cfy2012/memoria-os/simulator/shots/simulator_mobile.jpg

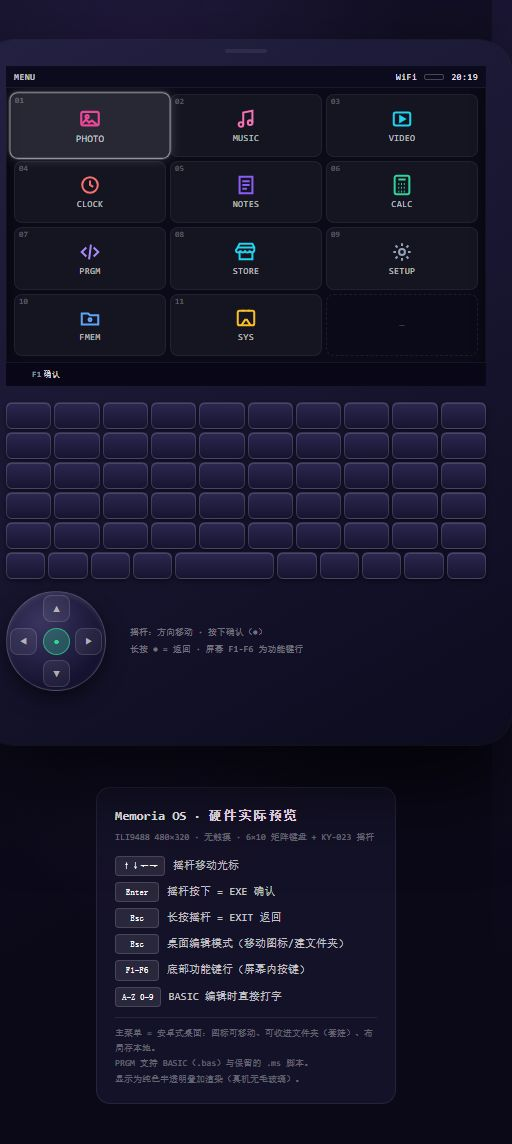
simulator/shots/simulator_mobile.jpg
