cfy2012/memoria-os/simulator/shots/simulator_desktop.jpg

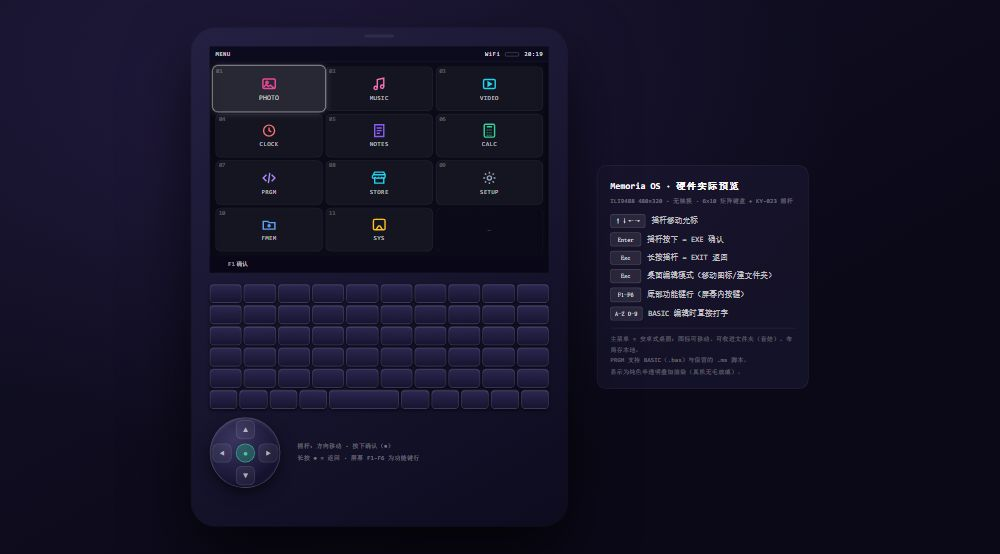
simulator/shots/simulator_desktop.jpg
