cfy2012/memoria-os/design/shell-design/Memoria-OS外壳尺寸规划.html

Memoria OS · HARDWARE SHELL · SPEC

# 外壳尺寸规划v7

ESP32-S3 掌机 · 2026-10-01 · 尺寸依据：HARDWARE-DIMENSIONS.md v7 · 引脚依据：components/memoria_drivers/include/drivers_config.hpp

核心板定版 摇杆甲案 KY-023 整机 ≈ 40.1mm 层间 2mm ×3

## 01关键尺寸

整机由 5 个实体层 + 3 条 2mm 悬空间隙叠成，屏幕面 → 背面。

40.1mm

整机厚度（设计值，38~42 区间）

2mm ×3

层间固定间隙（硬规则）

7.5mm

摇杆杆帽露出量

≥100 × 150mm

内腔净空（主板放置区）

## 02叠层剖面

每层高度 = 本层最高件（含板厚）；凸起元件收纳在本层内，不得侵占 2mm 间隙。实体隔板若加，每层 +1.6。

前面板

2.5

2

屏幕层

8

2

主板层

11.6

2

底仓

10

2

底壳

2

合计 ≈ 40.1mm（38~42 区间）
■ 主板层 11.6 = 洞洞板 1.6 + 摇杆机构 10（最高件）；核心板 5 / MCP23017 2.4 / TF 3 / TP4056 4 / 功放 5 / 灯带 2.5 全部收纳
■ 底仓 10 = 喇叭 8 + 腔体 2；锂电 5 平放
■ 屏幕层 8 = ILI9488 含排针（上限，实测可压到 6~7）

摇杆杆帽穿透（甲案 KY-023）

摇杆 PCB 面 → 前面板外表面 = 机构 10 + 间隙 2 + 屏幕层 8 + 间隙 2 + 面板 2.5 = 24.5mm 壳内贯通。
杆帽总高 32mm（自 PCB 面）→ 从前面板孔 Ø14~16 露出 7.5mm 作握持头。
屏幕 PCB 56×91 仅占屏幕层部分，摇杆走 PCB 侧边通道，不与屏体干涉；贯通路径上不得有金属屏蔽件。

ESP32 形态：核心板定版

S3-Zero 类核心板 18×27×4.5~5，插针/排母装配，免自焊 RF，自带屏蔽罩天线免净空区。
主板层独立小舱按 20×30 预留。模组直焊方案已弃用（需自焊 RF + 天线端 5mm 禁金属）。

## 03器件尺寸清单

典型值为市售模块通用规格，定稿前以卡尺实测为准（见 §07）。

器件 | 平面占位 | 高度 | 所在层 | 安装 | 外壳相关
ESP32-S3 核心板（S3-Zero 类）定版 | 18 × 27 | 4.5~5 | 主板层 | 插针/排母 | 小舱 20×30；免自焊 RF
ILI9488 3.5″ 屏模块 | PCB 56 × 91 | 6~8 含排针 | 屏幕层 | 排针插主板 | 视窗 70.8×48.5；屏幕窗 ≥71×49；务必实测
2× MCP23017（键盘扩展）最终定版 | 10.5 × 7.6 ×2 | 2.4 | 主板层 | 贴片/模块 | I2C 1/6，0x20/0x21，无 INT
轻触开关 6×6 矮款 ×60 | 6 × 6 | 2.5 | 主板层 | 直插 | 键中心距 10（≥9）；键孔 4.5×4.5
KY-023 摇杆高度约束 | PCB 26 × 34 | 板件 ~10 总高 ~32 | 主板层 | 直插 | 杆帽穿顶露出 7.5mm；面板孔 Ø14~16
MAX98357A 功放 | 15.5 × 13 | 4~5 | 主板层 | 模块 | 就近焊喇叭侧，引线短
喇叭 3W 4Ω | 23×35 或 20×30 | 5~10 +腔 2~3 | 底仓 | 粘/螺丝 | 透音孔开在喇叭正对面
TF 卡座（焊接式） | 15 × 16 | 2~3 | 主板层 | 焊接 | 卡外露 ≥4mm；侧缝 ≥13×2；可拆卸拔卡
SD 大卡槽（预留选项） | 30 × 29 | 3.5 | 主板层 | — | 侧缝 25×2.5；插卡行程 5mm；是否预留待定
TP4056 USB-C 充电模块 | 26.5 × 17.5 | 3~4 | 主板层 | 模块 | USB-C 凸出板边 1.5~2；侧孔 10×4
锂电聚合物 503450 级 | 50 × 34 | 5 | 底仓 | 松配 | 每边预留 1mm；仓按实物复核
WS2812 灯带 ×2 | 宽 10 | 2.5 | 主板层边缘 | 粘 | 每条 6 珠 ≈55mm；走线槽
电源拨动开关 SS12D00 | 19 × 10 | 7 含柄 | 侧壁 | — | 侧壁开槽 19×10；柄行程 4
主板洞洞板 | 100 × 150 | 板厚 1.6 | 主板层 | — | 元件层净高 ≤2

## 04前面板 / 侧壁开孔

全部开孔在壳体建模时按本表预留。

孔位 | 尺寸 | 位置 | 说明
屏幕窗 | ≥71 × 49 | 前面板 | 3.5″ ILI9488 480×320；实测视窗 +0.5
摇杆孔 | Ø14~16 | 前面板 | KY-023 杆帽穿顶贯通，露出 7.5mm
麦克风孔 | Ø1 × 2~3 | 前面板边缘 | INMP441 拾音（预留 GPIO45）
侧键孔 | ~20 × 3 | 侧壁 | 音量 / 电源
USB-C | 10 × 4 | 侧壁 | TP4056 充电口凸出 1.5~2
TF 卡 | ≥13 × 2 | 侧壁 | 卡外露 ≥4mm，可拆卸拔卡（字库/音频换卡）
SD 大卡槽（若预留） | 25 × 2.5 | 侧壁 | 插卡行程 5mm；待确认
电源开关槽 | 19 × 10 | 侧壁 | 柄行程 4mm
烧录口 / 排针孔 | 待定 | 侧壁或底壳 | UART 唯一烧录通道（43/44），必须预留
键盘键孔 | 4.5 × 4.5 ×60 | 前面板键盘区 | 6×10 布局，键中心距 10
喇叭透音孔 | 按喇叭面 | 底壳/侧壁 | 开在喇叭正对面

## 05GPIO / I2C 参考（迁移后）

引脚唯一来源：components/memoria_drivers/include/drivers_config.hpp。

功能 | GPIO | 说明
摇杆 X / Y | 7（ADC1_CH6）/ 5（ADC1_CH4） | 迁移后；旧 36/37 被 PSRAM 占
摇杆 BTN | 38 | 不动
电池 ADC | 4（ADC1_CH3） | 迁移后；旧 39 无 ADC
TF 卡 CS | 17 | 迁移后；旧 5
I2S BCLK / WS / DOUT | 18 / 21 / 15 | 迁移后；旧 4/3/2
SPI SCLK / MOSI / MISO | 12 / 11 / 13 | 不动
屏幕 CS / DC / RST / BLK | 10 / 9 / 8 / 14 | 不动
键盘灯带 | 46（RMT） | 不动
麦克风（预留） | 45 + 16/47（或 48） | INMP441；strapping 谨慎
USB D- / D+ | 19 / 20 | OTG 占用 → UART 为唯一烧录通道
UART0 TX / RX | 43 / 44 | 控制台 / 烧录
自由脚 | 16 / 47 / 48 + 40 / 41 / 42 | 可用 GPIO
永久不可用 | 26~32（Flash）、33~37（PSRAM） | 物理接不出

I2C 总线（I2C_NUM_0 @ GPIO1/6，400kHz）

0x20 / 0x21 = MCP23017 ×2（行+列C0-C3 / 列C4-C9）最终定版；
0x18 / 0x68 / 0x6B 预留段（新器件接线前请核对 I2C 地址占用）。

## 06装配顺序（底 → 顶）

5 步合壳，每层间留 2mm 悬空（支柱/卡扣），需要实体隔板时每层 +1.6。

1

#### 底壳 + 底仓

锂电 503450 平放（每边 1mm 松配）、喇叭 3W 定位，透音孔对正。

2

#### 主板层

洞洞板 100×150 固定；核心板插排母（小舱 20×30）；摇杆 KY-023 直插；MCP23017×2、TF 座、TP4056、MAX98357A、灯带走线槽。

3

#### 屏幕层

ILI9488 排针朝下插入主板对应排母，屏幕窗对位；摇杆杆帽走 PCB 侧边通道。

4

#### 前面板

60 键孔对位；摇杆杆帽从 Ø14~16 孔穿出，露出 7.5mm；屏幕窗合位。

5

#### 合盖 + 侧壁件

USB-C（10×4）、TF（≥13×2 外露 4mm）、电源开关槽、烧录口对孔；开机自检。

## 07待卡尺实测（定稿前必测）

以下 4 项是市售典型值，实际偏差会直接改变整机厚度或露出量。

- ILI9488 模块含排针实际高度 — 6~8mm，直接影响整机厚度 ±2mm （对应屏幕层 8）
- 喇叭实际厚度 + 腔体余量 — 5~10 + 2~3 （对应底仓 10）
- KY-023 杆帽立起实际总高 — 32±，偏差影响露出量 7.5± （对应摇杆穿顶）
- 电池实际厚度 — 503450 级典型 5，仓按实物复核 （对应底仓）

数据源：HARDWARE-DIMENSIONS.md v7 · components/memoria_drivers/include/drivers_config.hpp

Memoria OS · shell-design v7 · 2026-10-01
