cfy2012/memoria-os/docs/EASTER-EGGS-SPEC.md

# Memoria OS 彩蛋清单（Easter Eggs SPEC）

> 用途：给 GLM 实施用。共 100 条，时间线覆盖「送出之日 → 高一开学前」。
> **设计铁律（违反视为失败）**：
> 1. **发现式**——彩蛋是被使用者主动触发的，不是被推送的；
> 2. **非抢占**——任何彩蛋不得打断正在进行的操作，不得抢焦点、不得挡输入；
> 3. **可关闭**——设置页提供「彩蛋开关」，关掉后全部彩蛋失效；
> 4. 日期类彩蛋需 NVS 标记防重复（一年只触发一次），避免每次开机都弹。
> **受众口径**：使用者为同龄人（初三），**不以儿童视角设计**；文案平等、有梗、不幼稚。
> **暂缓项**：原「情人节画心」彩蛋按用户要求暂缓（赠礼双方为异性，语境不适用），未列入；后续如需启用由用户决定。

## 一、日期/时间触发（时间线彩蛋）17 条

| 编号 | 名称 | 触发方式 | 呈现效果 | 实现要点 |
|---|---|---|---|---|
| 1 | 首启欢迎 | 系统第一次开机 | 专属欢迎页「这是你的第二大脑」 | NVS 标记 has_booted，仅首次 |
| 2 | 第 7 天 | 累计开机天数 = 7 | 「你已经用它 7 天了」小横幅 | NVS 记 boot 计数 |
| 3 | 第 100 天 | 累计开机天数 = 100 | 计算器标题暂时显示「100 DAYS」 | NVS boot 计数 + 当天生效 |
| 4 | 万圣节 | 日期 10-31 | 图标南瓜/幽灵风一天；help 多一行 `trick or treat` | RTC 匹配 + 当日主题 |
| 5 | 平安夜 | 日期 12-24 | 时钟界面飘雪动画（纯氛围，不抢操作） | 时钟模式绘制雪粒子 |
| 6 | 圣诞 | 日期 12-25 | 圣诞配色一天 + 隐藏命令 `santa` | RTC + 主题色表 |
| 7 | 跨年 | 12-31 23:59 | 时钟界面倒计时，归零像素烟花 | 时钟模式专用分支 |
| 8 | 春节 | 农历正月初一（预置年份表） | 红色主题 + 隐藏命令 `红包` 随机文案 | 需农历年份映射表（GLM 配 2026/2027） |
| 9 | 清明 | 日期 4-04±1 | 当天首启显示「思」静默屏一秒 | 非抢操作，boot 横幅位 |
| 10 | 劳动节 | 日期 5-01 | 启动画面「劳动最光荣」 | boot 横幅位 |
| 11 | 青年节 | 日期 5-04 | 启动画面「少年自有少年狂」 | boot 横幅位 |
| 12 | 儿童节 | 日期 6-01 | 启动画面「今日份的少年感已到账」 | boot 横幅位（同龄口径，不低幼） |
| 13 | 端午 | 农历五月初五（预置年份表） | 粽子像素画彩蛋 | 农历映射表 |
| 14 | 中考倒计时 | 6 月 1 日 → 中考日 | 开机横幅「距离中考还有 N 天，稳住」 | 中考日期可配置（默认当地 6 月下旬） |
| 15 | 开学前 | 日期 8-31 | 隐藏命令 `要开学了` →「暑假余额不足」 | 隐藏命令即可，无需日期匹配 |
| 16 | 使用者生日 | 日期 2-01（默认预置，NVS 可改） | 开机横幅「生日快乐」+ 像素蛋糕（一年一次） | RTC 匹配 + NVS 年份标记 |
| 17 | 深夜关怀 | 23:00 后首次开机 | 「这么晚还不睡？明天上课」 | 时间匹配 + 一天一次 |

## 二、shell 隐藏命令（拉丁/致敬/内行梗）18 条

| 编号 | 名称 | 触发方式 | 呈现效果 | 实现要点 |
|---|---|---|---|---|
| 18 | memento | shell 敲 `memento` | 你写给使用者的寄语 | 隐藏命令，不进 help 清单 |
| 19 | carpe diem | shell 敲 `carpe diem` | 随机一句鼓励文案 | 随机文案池 |
| 20 | sapere aude | shell 敲 `sapere aude` | 显示系统源码总行数统计 | 编译期宏或运行时统计 |
| 21 | ad astra | shell 敲 `ad astra` | 星星 ASCII 动画 | 逐帧输出 |
| 22 | veni vidi vici | shell 敲 `veni vidi vici` | 成就音效 + 已解锁彩蛋计数 | 彩蛋解锁记录表 |
| 23 | fortune | shell 敲 `fortune` | 随机格言/毒鸡汤（致敬 Unix） | 文案池 |
| 24 | sudo | shell 敲 `sudo` | 「你已是最权限，不需要这个」 | 一条回复 |
| 25 | rm -rf / | shell 敲 `rm -rf /` | 「想让我自毁？不，我很稳」 | 拦截真实 rm，回复彩蛋 |
| 26 | reboot -f | shell 敲 `reboot -f` | 「没必要，我很稳定」 | 拦截回复 |
| 27 | hack | shell 敲 `hack` | 「你被监控了……开玩笑的，安全区」 | 一条回复 |
| 28 | matrix | shell 敲 `matrix` | 绿字数字雨数秒（伪矩阵） | 全屏随机字符动画，可按键退出 |
| 29 | ghost | shell 敲 `ghost` | 「你发现我了！」幽灵闪现 | 一条回复 + 幽灵字符 |
| 30 | ping | shell 敲 `ping` | 「pong！」（网络致敬） | 一条回复 |
| 31 | whoami | shell 敲 `whoami` | 「你是这台机器的主人」 | 一条回复 |
| 32 | 42 | shell 敲 `42` | 「生命、宇宙以及一切的答案」（银河系漫游指南梗） | 一条回复 |
| 33 | 404 | shell 敲 `404` | 「你要找的彩蛋不存在（或者它不想被发现）」 | 一条回复 |
| 34 | bug | shell 敲 `bug` | 「这是特性，不是 bug」 | 一条回复 |
| 35 | hello world | shell 敲 `hello world` | 「你好，世界。你好，你。」 | 一条回复 |
| 36 | hug | shell 敲 `hug` | 像素字符拥抱动画 + 「抱一下，辛苦了」 | 一条回复 + 字符画 |

## 三、按键/计算器彩蛋 10 条

| 编号 | 名称 | 触发方式 | 呈现效果 | 实现要点 |
|---|---|---|---|---|
| 37 | Konami 码 | 任意界面：上上下下左右左右 BA | 屏幕角出现小幽灵跟随光标 | 键盘/摇杆输入序列识别 |
| 38 | 强迫症检测 | 连按回车 5 次 | 「你是有强迫症吗？」 | 按键计数窗口 |
| 39 | hello | 计算器输入 `0.7734` | 显示 `hello, world` | 计算器特殊值 |
| 40 | 学习机声明 | 计算器输入 `58008` | 「你想多了，这是学习机」 | 计算器特殊值 |
| 41 | 中考年 | 计算器输入 `2027` | 「中考加油！」 | 计算器特殊值 |
| 42 | 光速 | 计算器输入 `299792458` | 「光速。跑得比光快的是你的思维」 | 计算器特殊值 |
| 43 | 隐藏音效 | 特定双键同按 3 秒 | 播放隐藏音效 | 按键组合长按检测 |
| 44 | 心事检测 | 音量+ 连按 7 次 | 「按了 7 次，有什么心事？」 | 按键计数 |
| 45 | 模式大师 | 快速切换 5 个模式 | 「模式大师」解锁画面 | 短时模式切换序列 |
| 46 | 隐藏秒表 | 时钟界面长按确认键 | 打开隐藏秒表 | 长按检测 + 秒表 UI |

## 四、界面/系统彩蛋 11 条

| 编号 | 名称 | 触发方式 | 呈现效果 | 实现要点 |
|---|---|---|---|---|
| 47 | 开发者名单 | 版本号界面连点 10 次 | 开发者名单 + 感谢语 | 点击计数 |
| 48 | logo 翻转 | About 页点 3 次 logo | logo 翻转/变色 | 点击计数 + 动画 |
| 49 | 满电侠 | 电量 100% 时开机 | 「满电侠」称号显示 | boot 读电量 |
| 50 | 连续作战勋章 | uptime ≥ 24h | 时钟界面一枚「连续工作 24h」勋章 | uptime 检查 |
| 51 | 隐藏模式 | SAFE MODE 敲 help | 多一行「你发现了隐藏模式」 | SAFE MODE help 分支 |
| 52 | 空目录哲学 | 空目录 ls | 「这里什么都没有，除了……」随机一句 | ls 空目录分支 |
| 53 | 测试检测 | 语言设置来回切 3 次 | 「你是在测试我吗？」 | 切换计数 |
| 54 | 温度提醒 | 右下角连点 5 次 | 「你很烫，注意休息」 | 点击计数 |
| 55 | 关机告别 | 电量 0% 关机前 | 「我没电了，晚安」 | 低电量关机钩子 |
| 56 | 用眼关怀 | 连续使用 3 小时 | 「该休息了，眼睛会疼」 | 连续使用计时 |
| 57 | 听力关怀 | 音量调到最大 | 「耳朵会疼的」 | 音量上限提示 |

## 五、文件/存储彩蛋 8 条

| 编号 | 名称 | 触发方式 | 呈现效果 | 实现要点 |
|---|---|---|---|---|
| 58 | 秘密信 | `ls -a` 看到 `.secret` 目录 | 里面一封写给使用者的信 | 预置隐藏目录（ls 默认过滤点开头） |
| 59 | 给未来的你 | 打开 `README_给未来的你.txt` | 「开学也要加油」 | 预置文件 |
| 60 | 命名吐槽 | 新建文件命名为「测试」 | 「你确定叫这个？」 | 文件名检测 |
| 61 | 作业雷达 | 新建文件命名为「作业」 | 「在系统里找作业？写作业去吧」 | 文件名检测 |
| 62 | 系统自嘲 | 打开特殊命名文件夹（`.` 别名） | 系统自嘲文案 | 特殊路径拦截 |
| 63 | 温度确认 | 删除文件时二次确认 | 「这个文件可能很重要」 | 正常功能带温度文案 |
| 64 | 别打开 | 打开 `.do_not_open` 文件 | 「都说了别打开」 | 预置文件 + 名称拦截 |
| 65 | 彩蛋引导 | 存储使用率 ≥ 99% | 「清理一下，顺便看看 `.secret` 目录」 | 存储检查 + 引导提示 |

## 六、二十四节气彩蛋 24 条

| 编号 | 名称 | 触发方式 | 呈现效果 | 实现要点 |
|---|---|---|---|---|
| 66 | 立春 | 2-03/2-04 | 启动横幅「立春 · 万物生」 | 节气日期表（公历范围） |
| 67 | 雨水 | 2-18/2-19 | 「雨水 · 好雨知时节」 | 节气日期表 |
| 68 | 惊蛰 | 3-05/3-06 | 「惊蛰 · 春雷动，万物醒」 | 节气日期表 |
| 69 | 春分 | 3-20/3-21 | 「春分 · 昼夜平分」 | 节气日期表 |
| 70 | 清明 | 4-04/4-05 | 「清明 · 雨纷纷」 | 与 9 号同日，实施合并：静默屏 + 节气文案，一天一次 |
| 71 | 谷雨 | 4-19/4-20 | 「谷雨 · 雨生百谷」 | 节气日期表 |
| 72 | 立夏 | 5-05/5-06 | 「立夏 · 夏木成阴」 | 节气日期表 |
| 73 | 小满 | 5-20/5-21 | 「小满 · 物致于此小得盈满」 | 节气日期表 |
| 74 | 芒种 | 6-05/6-06 | 「芒种 · 有芒之种」 | 节气日期表 |
| 75 | 夏至 | 6-21/6-22 | 「夏至 · 日长之至」 | 节气日期表 |
| 76 | 小暑 | 7-06/7-07 | 「小暑 · 温风至」 | 节气日期表 |
| 77 | 大暑 | 7-22/7-23 | 「大暑 · 大热」 | 节气日期表 |
| 78 | 立秋 | 8-07/8-08 | 「立秋 · 秋至」 | 节气日期表 |
| 79 | 处暑 | 8-22/8-23 | 「处暑 · 出暑」 | 节气日期表 |
| 80 | 白露 | 9-07/9-08 | 「白露 · 露从今夜白」 | 节气日期表 |
| 81 | 秋分 | 9-22/9-23 | 「秋分 · 平分秋色」 | 节气日期表 |
| 82 | 寒露 | 10-07/10-08 | 「寒露 · 露寒而凝」 | 节气日期表 |
| 83 | 霜降 | 10-23/10-24 | 「霜降 · 气肃而凝」 | 节气日期表 |
| 84 | 立冬 | 11-07/11-08 | 「立冬 · 水始冰」 | 节气日期表 |
| 85 | 小雪 | 11-22/11-23 | 「小雪 · 未盛为雪」 | 节气日期表 |
| 86 | 大雪 | 12-06/12-07 | 「大雪 · 至此而雪盛」 | 节气日期表 |
| 87 | 冬至 | 12-21/12-22 | 「冬至 · 冬至不端饺子碗，冻掉耳朵没人管」 | 节气日期表（北方梗） |
| 88 | 小寒 | 1-05/1-06 | 「小寒 · 雁北乡」 | 节气日期表 |
| 89 | 大寒 | 1-20/1-21 | 「大寒 · 至此极」 | 节气日期表 |

## 七、模式专属彩蛋 6 条

| 编号 | 名称 | 触发方式 | 呈现效果 | 实现要点 |
|---|---|---|---|---|
| 90 | 整点报时 | 时钟模式每逢整点 | 「X 点整」+ 可选音效 | 整点检测，轻量，不抢操作 |
| 91 | 单曲计数 | 音乐模式同一首歌播放 ≥3 次 | 「这首你听了 N 遍了」 | NVS 播放计数 |
| 92 | 照片故事 | 照片模式查看特定日期（如送出日）的照片 | 「这天有故事」 | 文件名/EXIF 日期匹配 |
| 93 | 秘密程序 | 编程模式运行 `secret.bas` | 隐藏程序：像素动画 | 预置脚本 + 名称拦截 |
| 94 | 隐藏商品 | 商店模式出现 0 元商品「开发者纪念头像」 | 可购买收藏 | 商店数据预置 |
| 95 | 笔记彩蛋 | 笔记标题输入「memento」 | 套用隐藏模板（一句寄语） | 标题关键词匹配 |

## 八、成就系统彩蛋 5 条

| 编号 | 名称 | 触发方式 | 呈现效果 | 实现要点 |
|---|---|---|---|---|
| 96 | 百炼成钢 | 累计开机 100 次 | 「百炼成钢」成就 | NVS 开机计数 |
| 97 | 键盘侠 | 累计敲命令 1000 次 | 「键盘侠」成就 | NVS 命令计数 |
| 98 | 全勤奖 | 连续 7 天开机 | 「全勤奖」成就 | NVS 日期链检测 |
| 99 | 寻宝猎人 | 解锁彩蛋 ≥ 10 个 | 「寻宝猎人」称号 | 解锁记录表 |
| 100 | 满级大佬 | 解锁全部彩蛋 | 「你已经找到所有秘密」+ 最后一封信 | 全解锁检测 |

## 实施说明

- **农历节日（8/13）**：GLM 需配 2026/2027 年份农历映射表（春节、端午具体公历日期），RTC 公历日期查表触发。
- **中考倒计时（14）**：中考日期做成可配置字段（NVS/配置文件），默认按当地中考时间（2027 年 6 月下旬）；提前 30 天进入倒计时窗口，只显示一次/天。
- **NVS 防重复**：所有日期类彩蛋配「年份已触发」标记，防止一天内多次重启反复弹出；生日彩蛋单独按年份标记；深夜关怀（17）按「当天已触发」标记。
- **优先级**：以上均属低优先级、纯增量模块，建议在系统主线稳定（240MHz 验收完成、教材/手册同步完成）后排期实施。
- **彩蛋开关**：设置页加「彩蛋」开关，默认开；关闭后隐藏命令返回 unknown command，日期类不触发，按键类不识别。
- **口径**：所有文案按同龄人（初三）平等语气撰写，杜绝「小朋友」「乖」等低幼表述；发现者读到的是「伙伴」，不是「长辈」。

## 验收口径

1. 彩蛋开关关闭后，全部 64 条失效；
2. 任何彩蛋不得阻塞正在进行的操作（渲染/输入/任务）；
3. 日期类彩蛋一年内同一天只出现一次；
4. 隐藏命令不在 help 清单出现（51 号彩蛋除外，它自己就是被发现项）；
5. 全部文案通过「同龄人口径」审查：无低幼化、无性别敏感内容；
6. 节气彩蛋 24 条全年覆盖，与日期类彩蛋同天时合并为一次触发（如清明）；
7. 成就系统依赖 NVS 解锁记录表，与 22 号（veni vidi vici）共用同一计数。
