cfy2012/memoria-os/docs/_drafts/human-story.md

# README「人情味」素材草稿（供 GLM 整合，不直接照抄）

> 生成：2026-10-01 · 豆包-1 供料。用途：README 重写时的「项目由来 / 致谢」叙事段。
> 素材是事实 + 用户原话碎片；整合时请按 GLM 的判断取舍、改写语气。**原则：平实、具体、不煽情、不 AI 腔；像一个人在讲自己做的机器，不像宣传稿。**

## 事实骨架（全部可查证）

- 项目名 **Memoria OS**——Memoria，记忆。这台机器最初的目的不是"做一个操作系统"，而是"做一台能送人的小电脑"。
- 收件人：一位女同学。她喜欢 BASIC，而且不把它当编程语言看——**她把程序当故事看**。
- 因为不同班，见面时间短，教学方式是"函授"：**三封信、四张纸正反面**，讲清楚面向过程 / 面向对象、程序的基本设计逻辑、行号是怎么回事。
- 信是照着《苏菲的世界》的路子写的——苏菲通过一封封信学哲学，她通过一封封信学编程。
- 她读完信说：**"跟平时不是一个人。"**——写信的人平时话不多，信里却把逻辑讲得又细又稳（写信人是信息学竞赛生，习惯严谨）。
- 这台机器上的 BASIC 解释器，就是为了让她能"读故事"——每行程序都是一句话，PRINT 是开口说话，IF..THEN 是选择，FOR..NEXT 是重复念叨。

### ChatLite 的由来（用户 2026-10-04 口述，chapter nine）

- 用户没有手机号、没有微信，QQ 有时候也崩溃——**经常跟人失联**。
- 所以他自己搭了个聊天网站，让别人拿网站跟他联系。**这个网站的源码就是 ChatLite。**
- 换句话说：ChatLite（以及现在掌机上的 chat 三端）不是练手项目，是作者解决自己真实通讯困境的实用工具——先给自己用，后来长成了掌机的聊天生态。

### 作者的自学之路（用户 2026-10-04 口述）

- 用户从 **2025 年 9 月**才开始学这些东西——一年前，连"API key"是什么都不知道。
- 一年里自学会的（按他自己的清单）：AI agent 与多 AI 并行协作、API / API key / DeepSeek 开发者、鸿蒙开发者、Android Studio、Arduino IDE、ESP-IDF、C++、HTTP/HTTPS、PHP、Python、JavaScript/CSS/HTML、Bash、CMD、Ubuntu Linux、Docker、Linux 设备树、虚拟机的使用与自制、制作 ISO 镜像、看 Arch Linux 源码。
- 这份清单是一条完整的楼梯：用 AI → 网页层 → 脚本层 → 通信层 → 硬件层 → 操作系统层。
- **叙事价值**：BASIC 教材写给零基础的人，而作者本人就是最好的第一个学员——他证明这条楼梯一年就能爬上来。

## 可用的"人味"句子（素材，不是定稿）

1. 开头一句可考虑：*"这台机器上跑的每一个字、每一行 BASIC，都是写给她看的。"*（若嫌重可换为更轻的表述）
2. 关于行号：*"行号不是古董，是信纸上的页码——让她知道故事从哪里继续。"*
3. 关于 GOTO 半禁用：*"GOTO 能用，但会提醒你：'跳来跳去，故事会乱。'"*（GOTO 半禁用机制的真实行为：用时报注意事项）
4. 关于死循环保护：*"FOR 循环有护栏——她写故事，不会写死。"*
5. 关于模拟器：*"固件之外还有个浏览器版，一样的东西，在电脑上也能先玩。"*

## 技术内容里可以留的"温度"点（与叙事不冲突）

- 11 个模式里有 PRGM（编程）——那是给她准备的书桌。
- 拼音输入法：打字给她发消息用的（若用户认可再写）。
- 键盘背光三条暖白档：夜里写程序不刺眼（若用户认可再写）。

## 语气红线（用户原话要求）

- 不要"AI 腔"：别用"赋能 / 生态 / 一站式 / 打造极致体验"这类词。
- 不要肉麻：不写"爱的结晶 / 深情之作"。
- 不煽情：事实摆出来，温度自然在。
- 成果归用户：README 的"作者"是用户，不是 AI。

## 结尾致谢（素材）

- 三方 AI（GLM / 豆包-1 / 豆包-2）协作开发：一个管固件主线，一个管解码，一个管外壳和文档——桥文件 AI-BRIDGE.md 里全是工作记录（如果 README 里要提，一句带过即可，别写成功劳簿）。
