cfy2012/memoria-os/design/键盘按键布局表.xlsx

ON/OFF | F1 | F2 | F3 | F4 | F5 | F6 | F7 | 背光 | Backspace
! 1 | @ 2 | # 3 | $ 4 | % 5 | ^ 6 | & 7 | * 8 | ( 9 | ) 0
- Q | _ W | E | R | T | Y | [ U | ] I | { O | } P
= A | + S | D | F | G | H | J | K | " L | : ;
Shift | \ Z | | X | C | V | B | / N | ? M | < , | > .
Capslock | Control | 音量减 | 音量加 | 空格 | LEFT | RIGHT | DOWN | UP | Enter
