cfy2012/memoria-os/docs/audio-guard/AudioGuard-最坏情况模拟.png

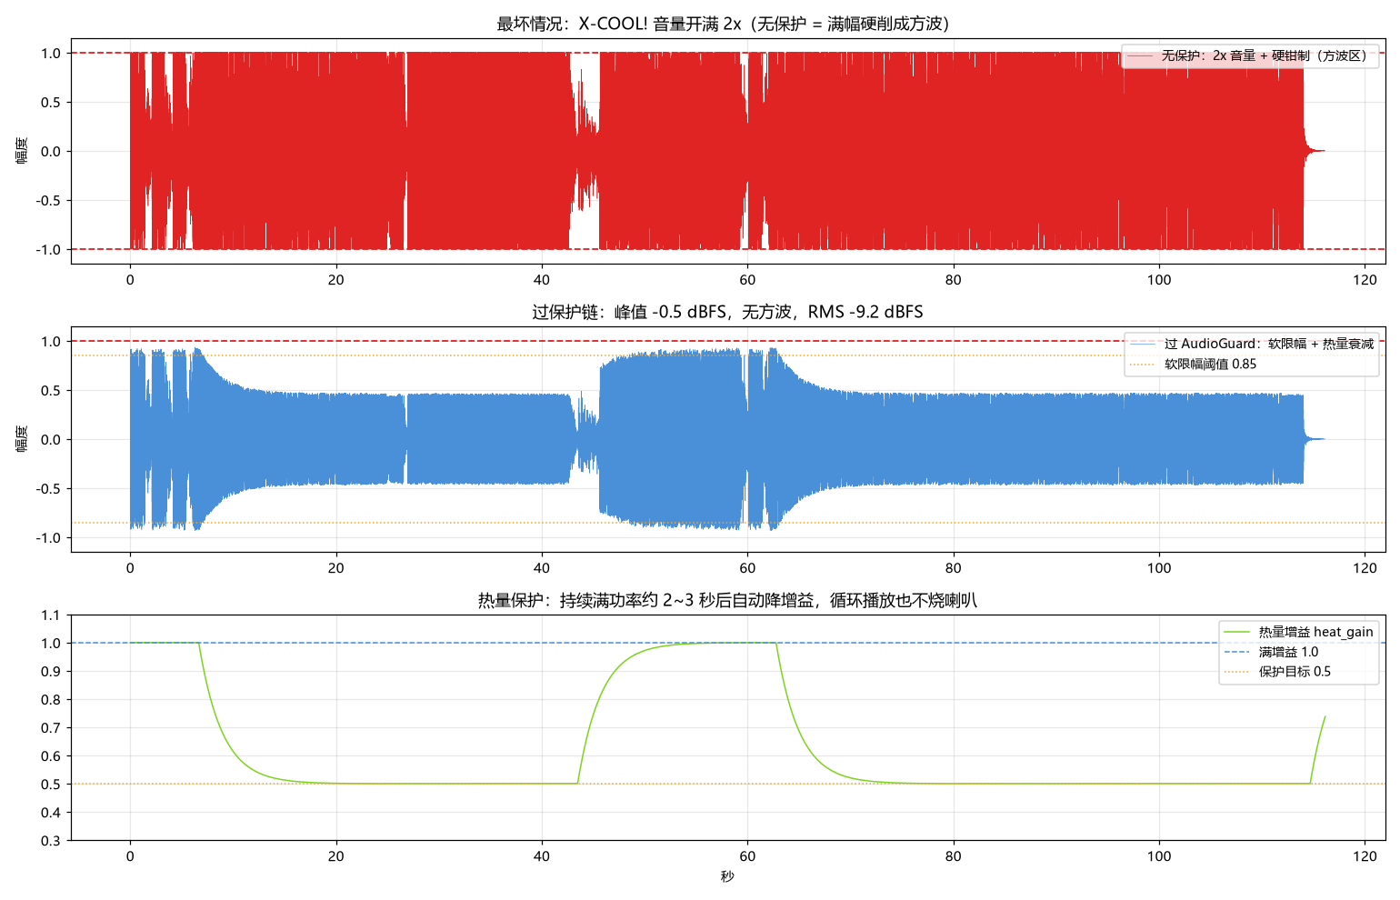
docs/audio-guard/AudioGuard-最坏情况模拟.png
