cfy2012/memoria-os/docs/audio-guard/BATIDAO-FUNK-波形分析.png

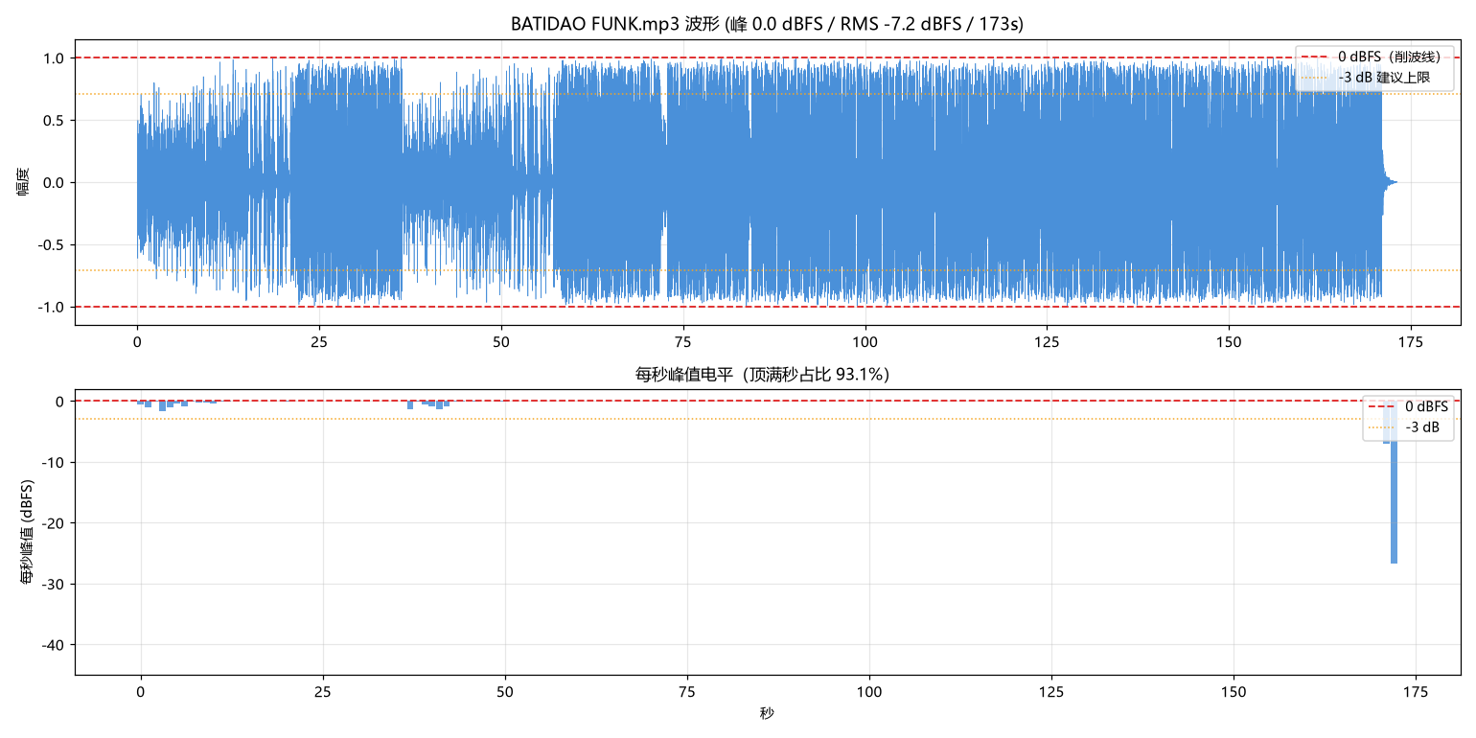
docs/audio-guard/BATIDAO-FUNK-波形分析.png
