cfy2012/memoria-os/docs/audio-guard/DANÇA-DO-VERÃO-波形分析.png

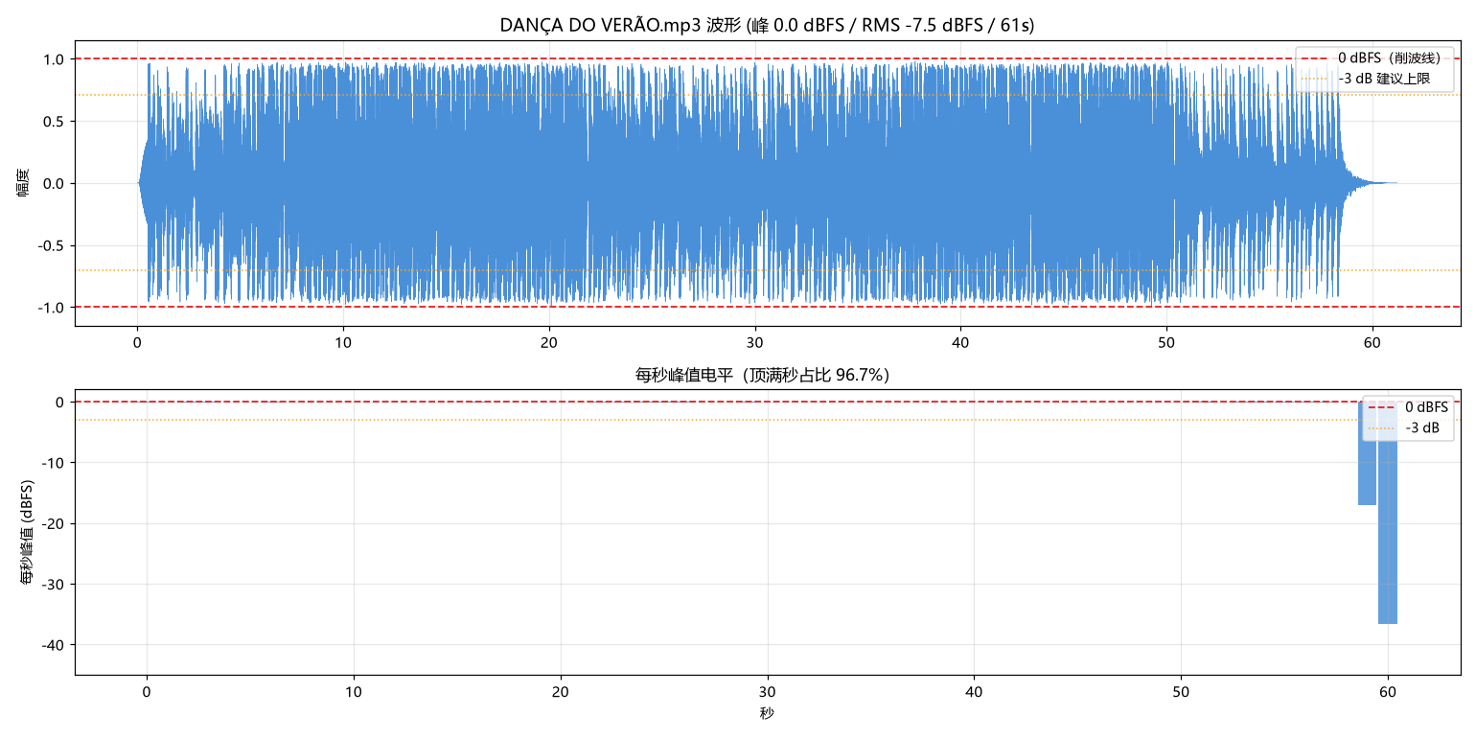
docs/audio-guard/DANÇA-DO-VERÃO-波形分析.png
