cfy2012/memoria-os/docs/audio-guard/De-Natal-波形分析.png

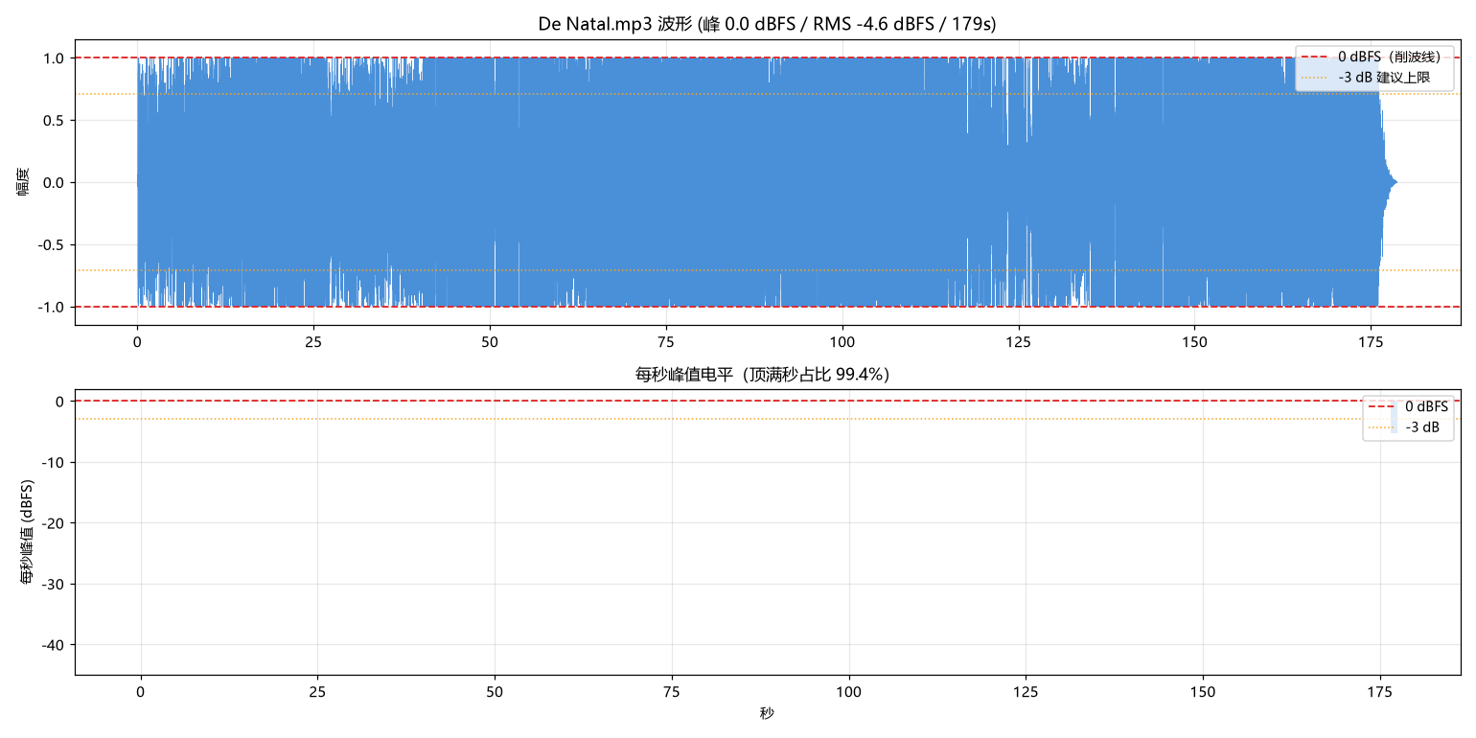
docs/audio-guard/De-Natal-波形分析.png
