cfy2012/memoria-os/docs/audio-guard/DREAMFUNK-波形分析.png

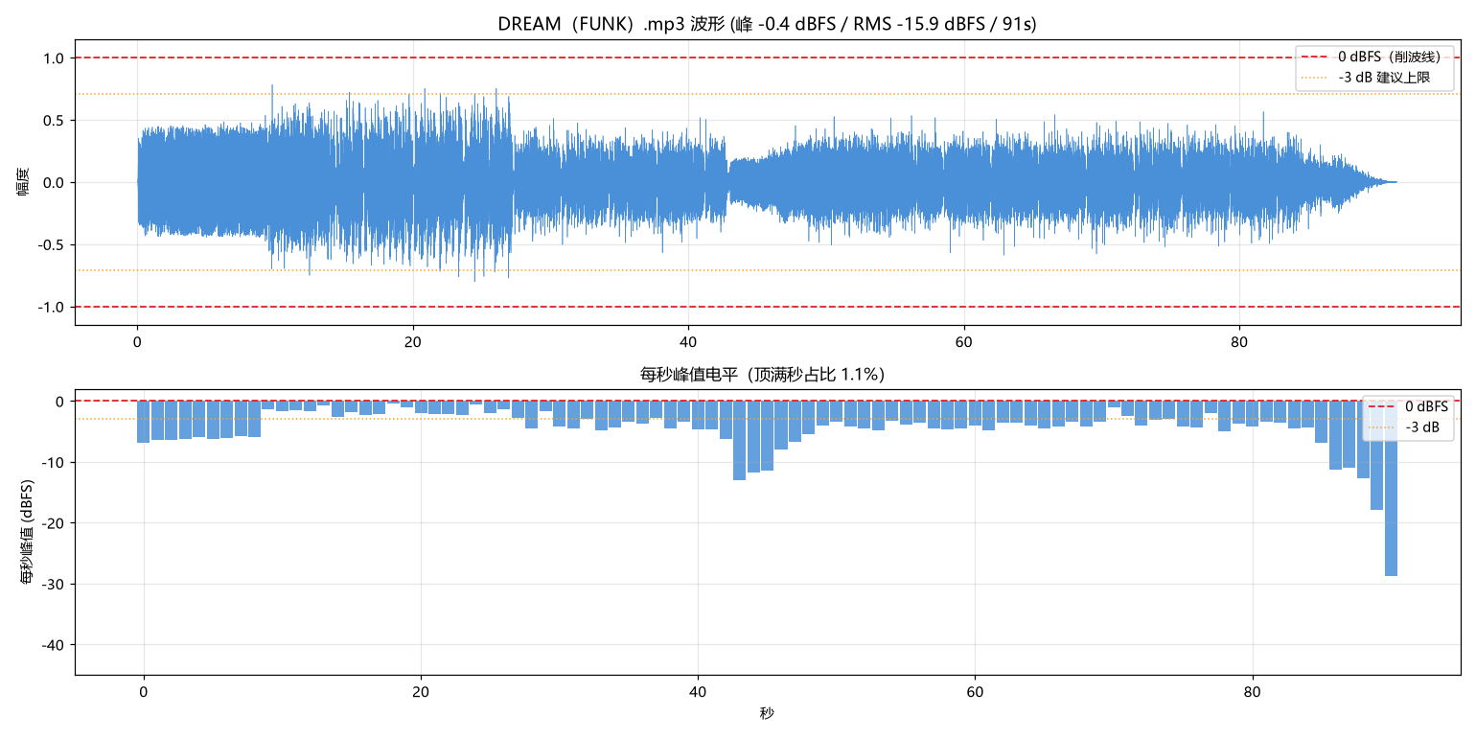
docs/audio-guard/DREAMFUNK-波形分析.png
