cfy2012/memoria-os/docs/audio-guard/FAVELA-波形分析.png

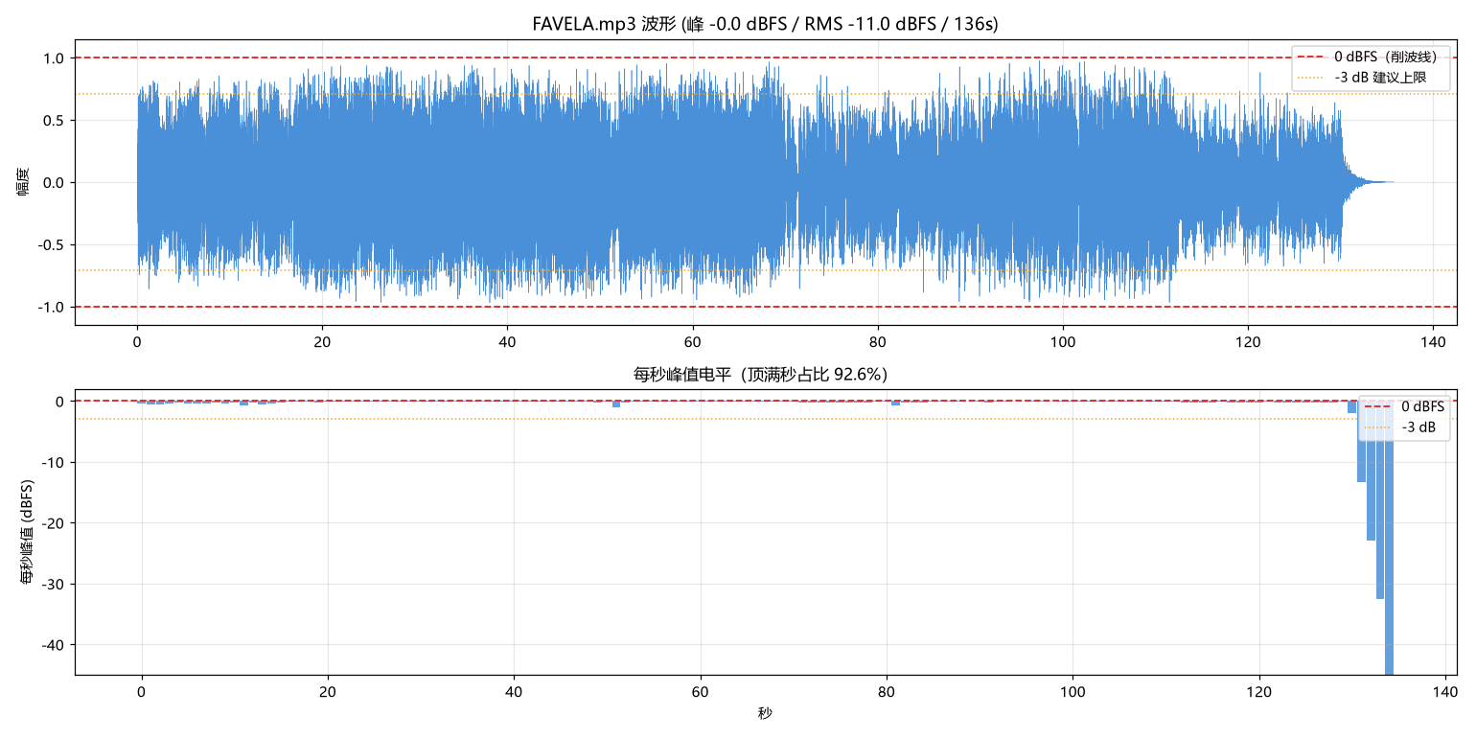
docs/audio-guard/FAVELA-波形分析.png
