cfy2012/memoria-os/docs/audio-guard/FREQUÊNCIA-波形分析.png

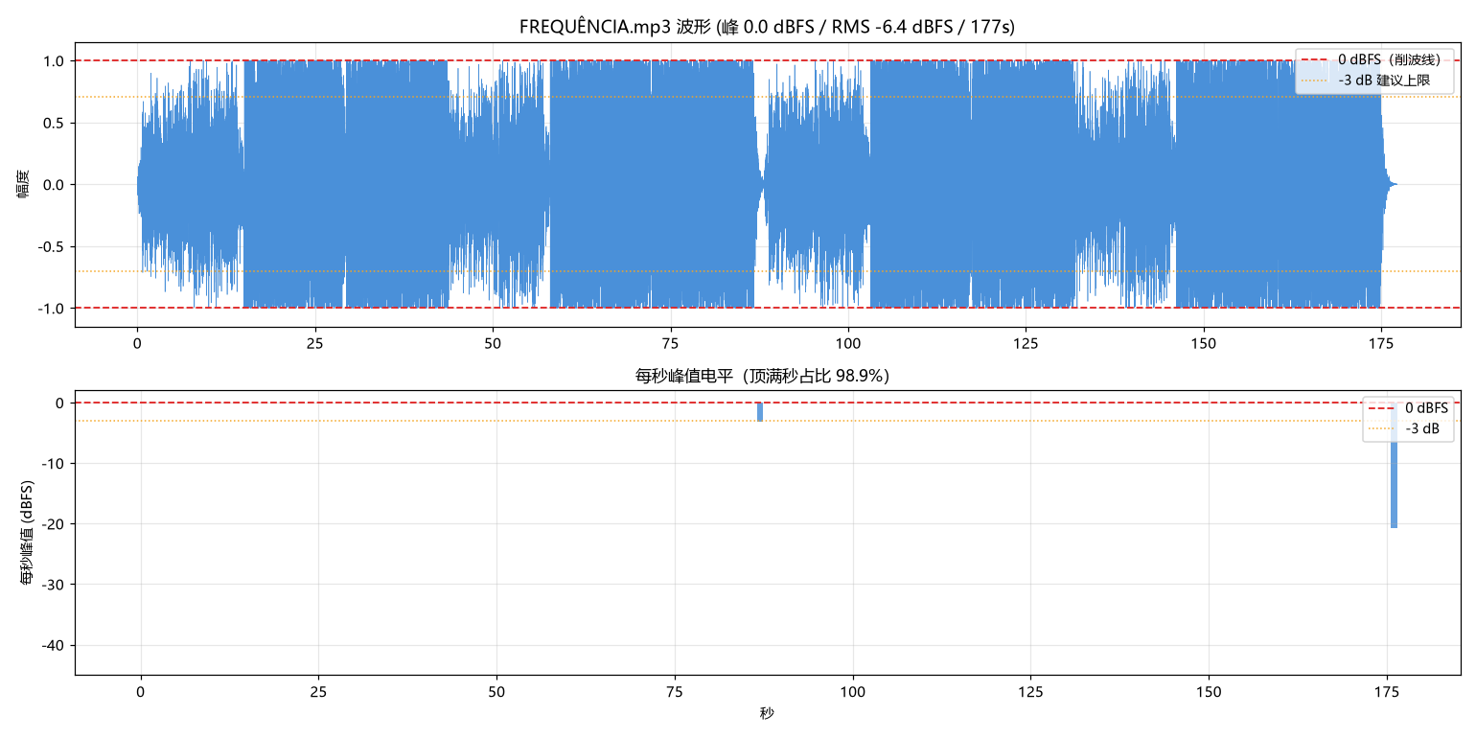
docs/audio-guard/FREQUÊNCIA-波形分析.png
