cfy2012/memoria-os/docs/audio-guard/HEAVENLY-JUMPSTYLE-波形分析.png

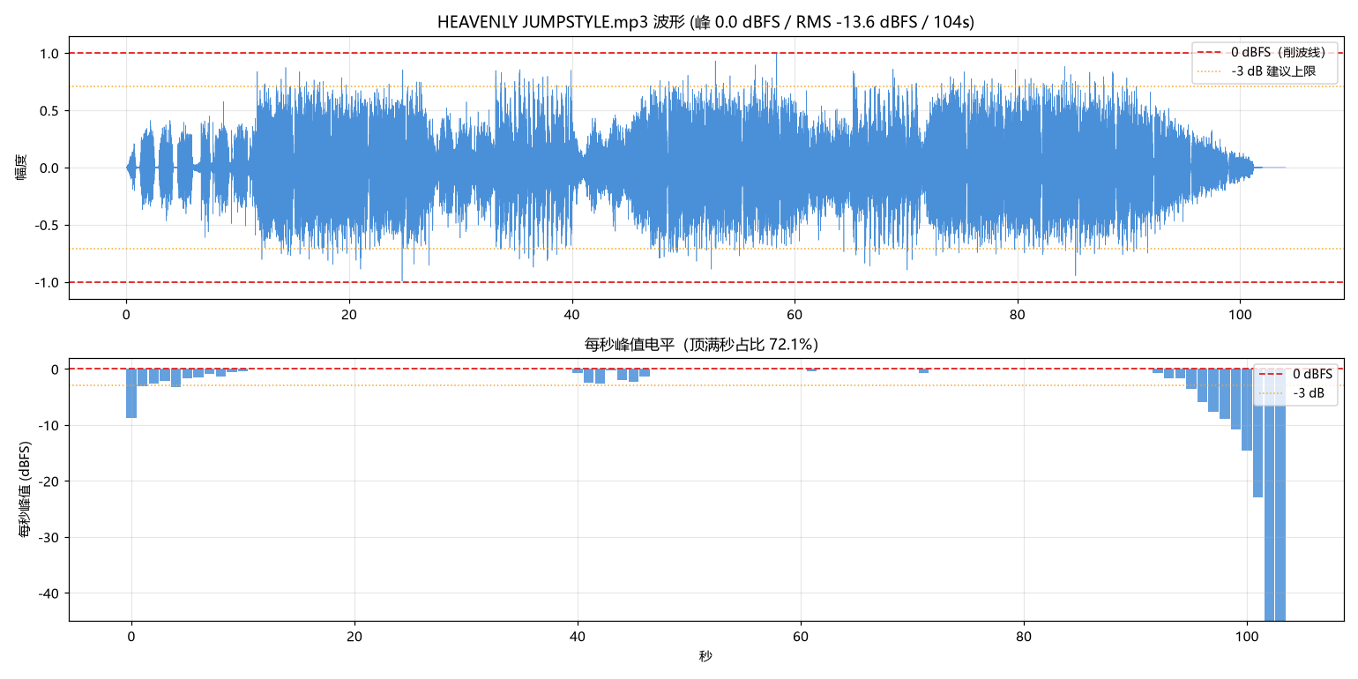
docs/audio-guard/HEAVENLY-JUMPSTYLE-波形分析.png
