cfy2012/memoria-os/docs/audio-guard/HOMAGE-FUNK-波形分析.png

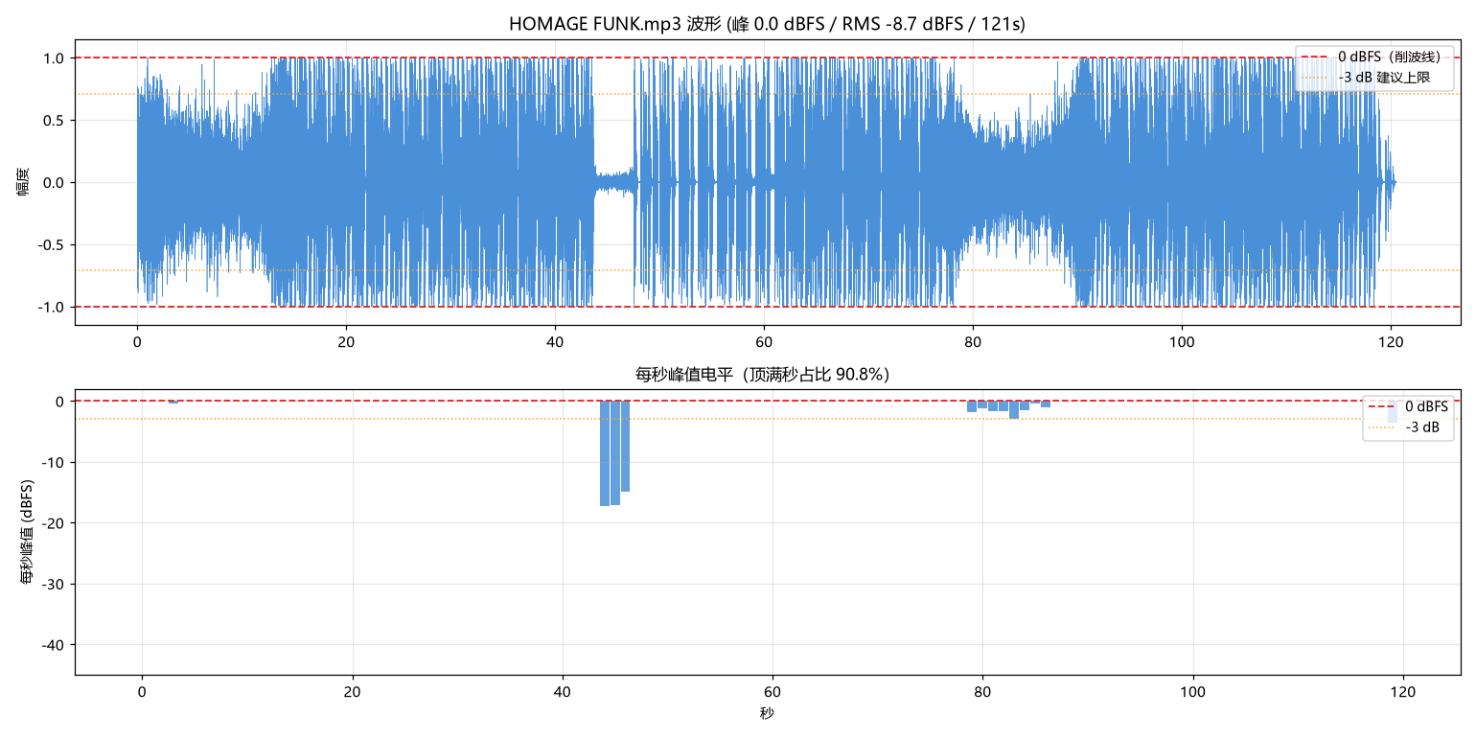
docs/audio-guard/HOMAGE-FUNK-波形分析.png
