cfy2012/memoria-os/docs/audio-guard/Luvsic-波形分析.png

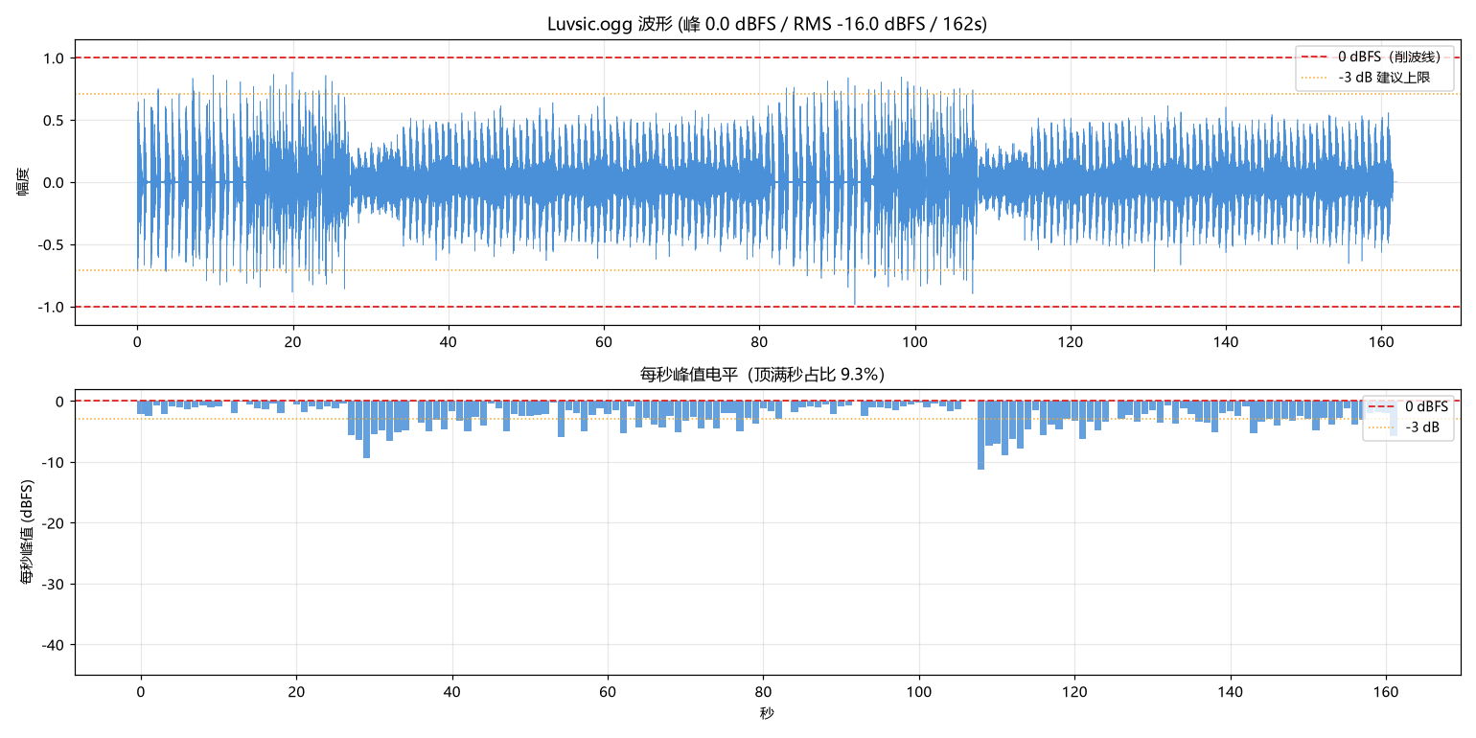
docs/audio-guard/Luvsic-波形分析.png
