cfy2012/memoria-os/docs/audio-guard/Marisama-ECLIPSER-Super-Slowed-波形分析.png

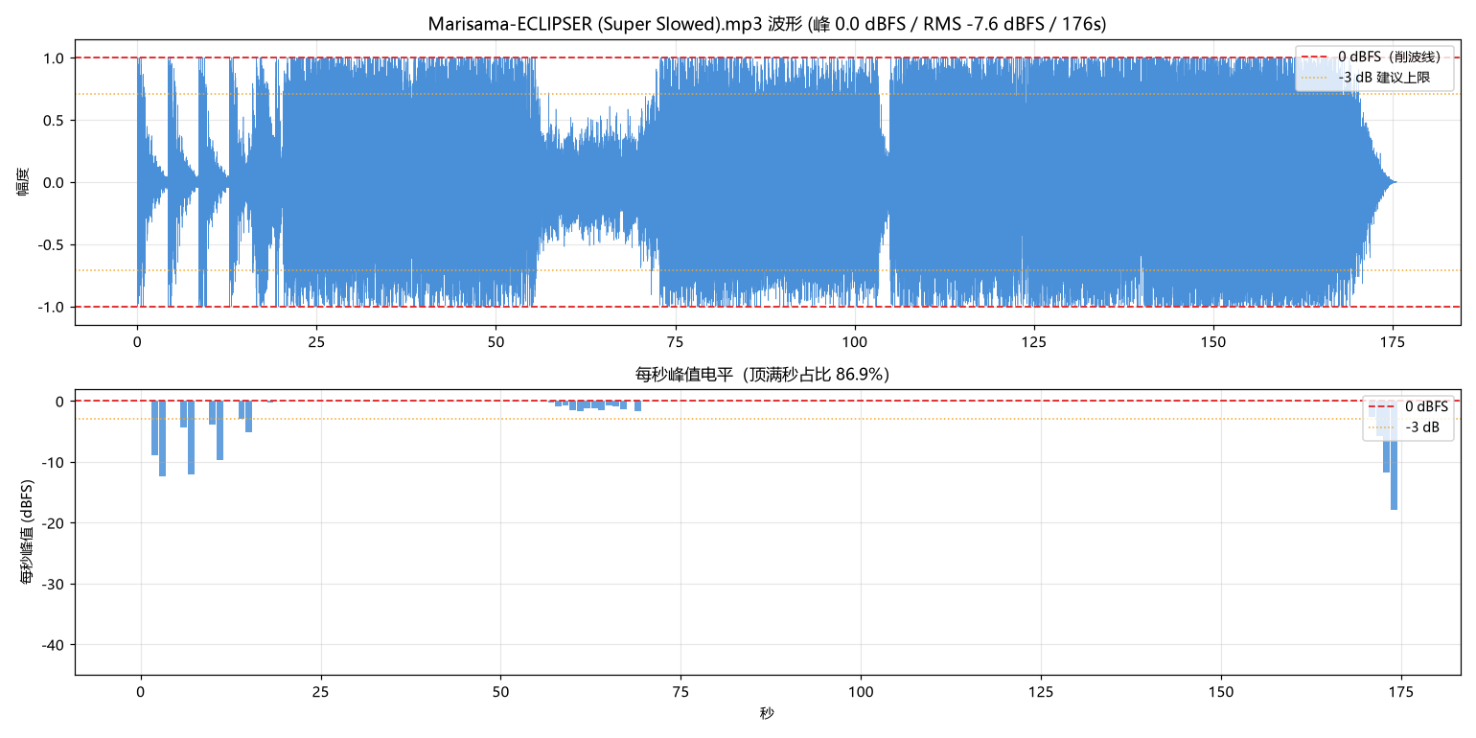
docs/audio-guard/Marisama-ECLIPSER-Super-Slowed-波形分析.png
