cfy2012/memoria-os/docs/audio-guard/MI-RESPIRAR-波形分析.png

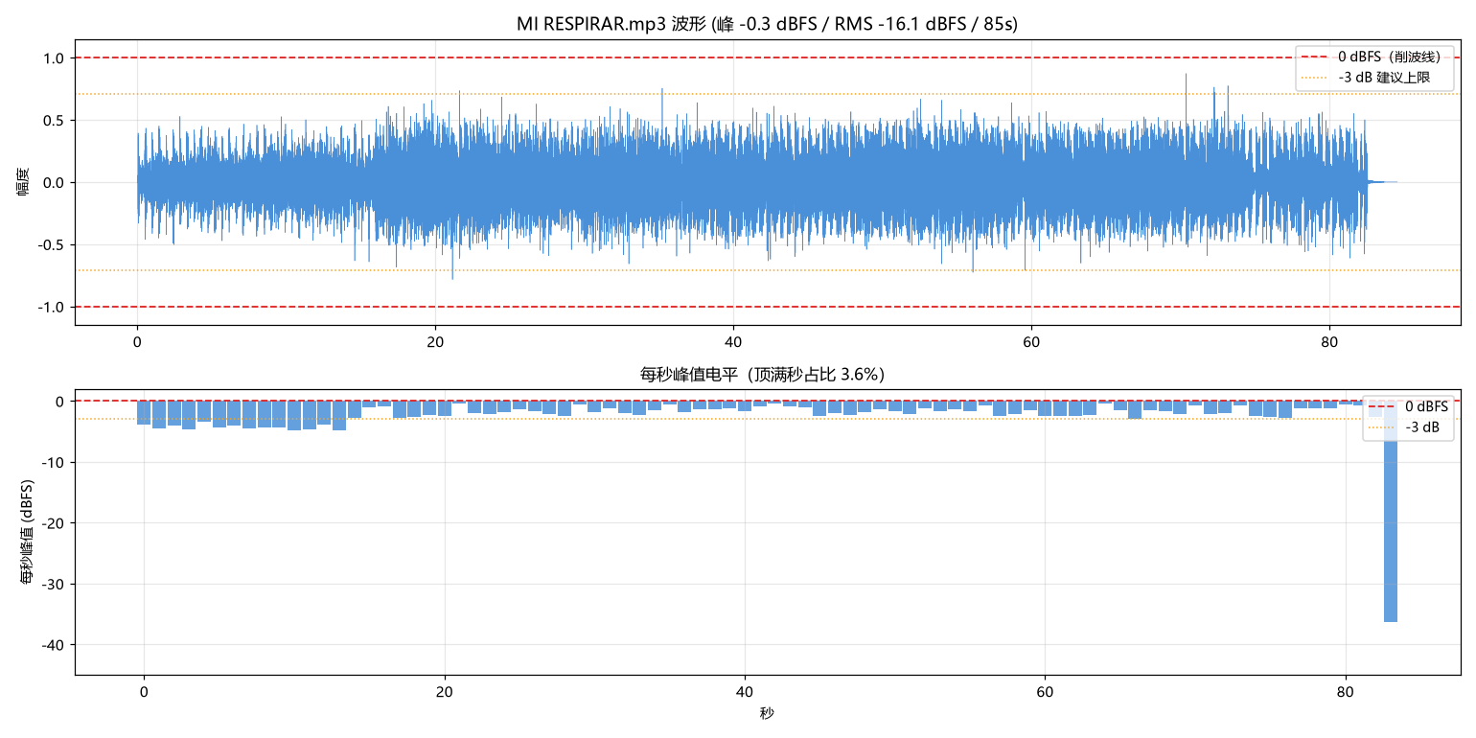
docs/audio-guard/MI-RESPIRAR-波形分析.png
