cfy2012/memoria-os/docs/audio-guard/Ngẫu-Hứng-波形分析.png

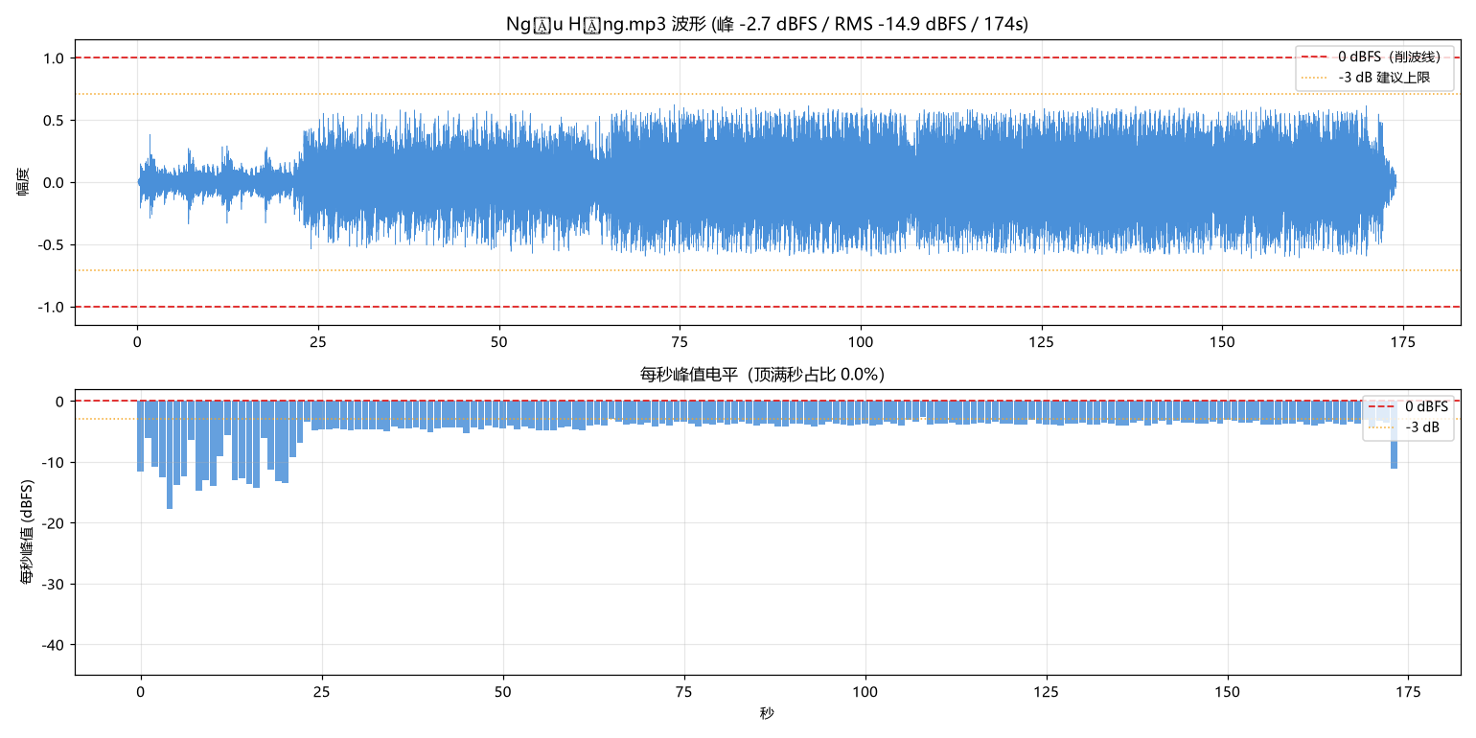
docs/audio-guard/Ngẫu-Hứng-波形分析.png
