cfy2012/memoria-os/docs/audio-guard/NO-BATIDAO-波形分析.png

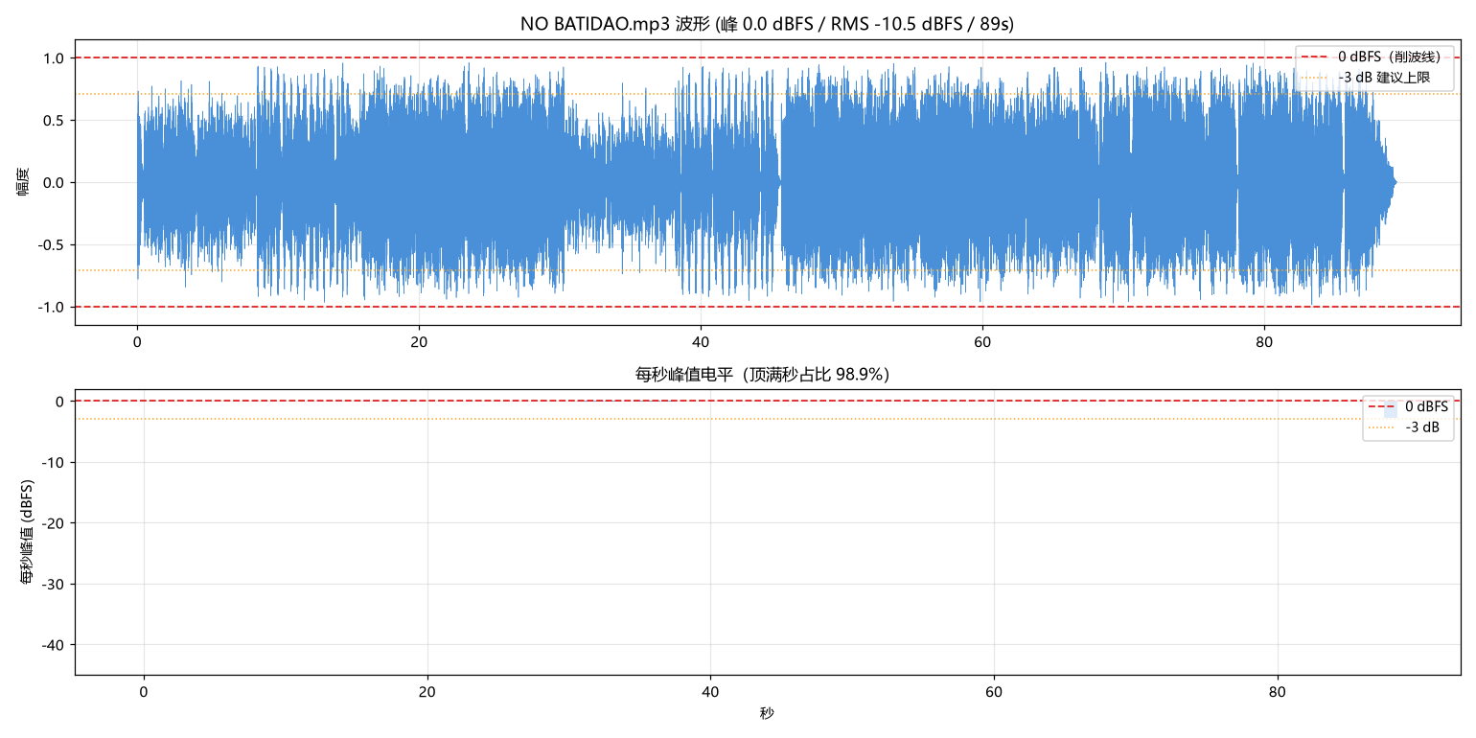
docs/audio-guard/NO-BATIDAO-波形分析.png
