cfy2012/memoria-os/docs/audio-guard/NO-ERA-AMOR-波形分析.png

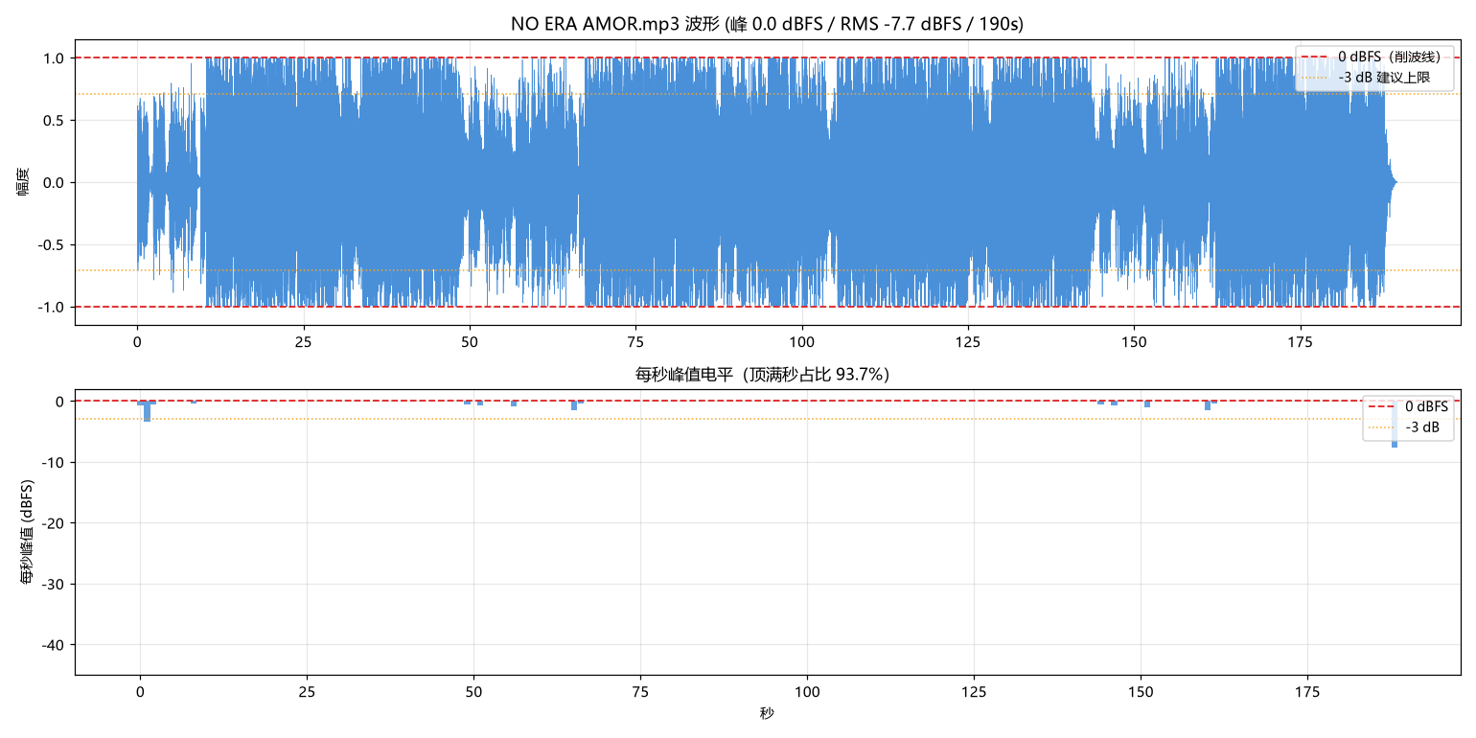
docs/audio-guard/NO-ERA-AMOR-波形分析.png
