cfy2012/memoria-os/docs/audio-guard/OneRepublic-Good-Life-波形分析.png

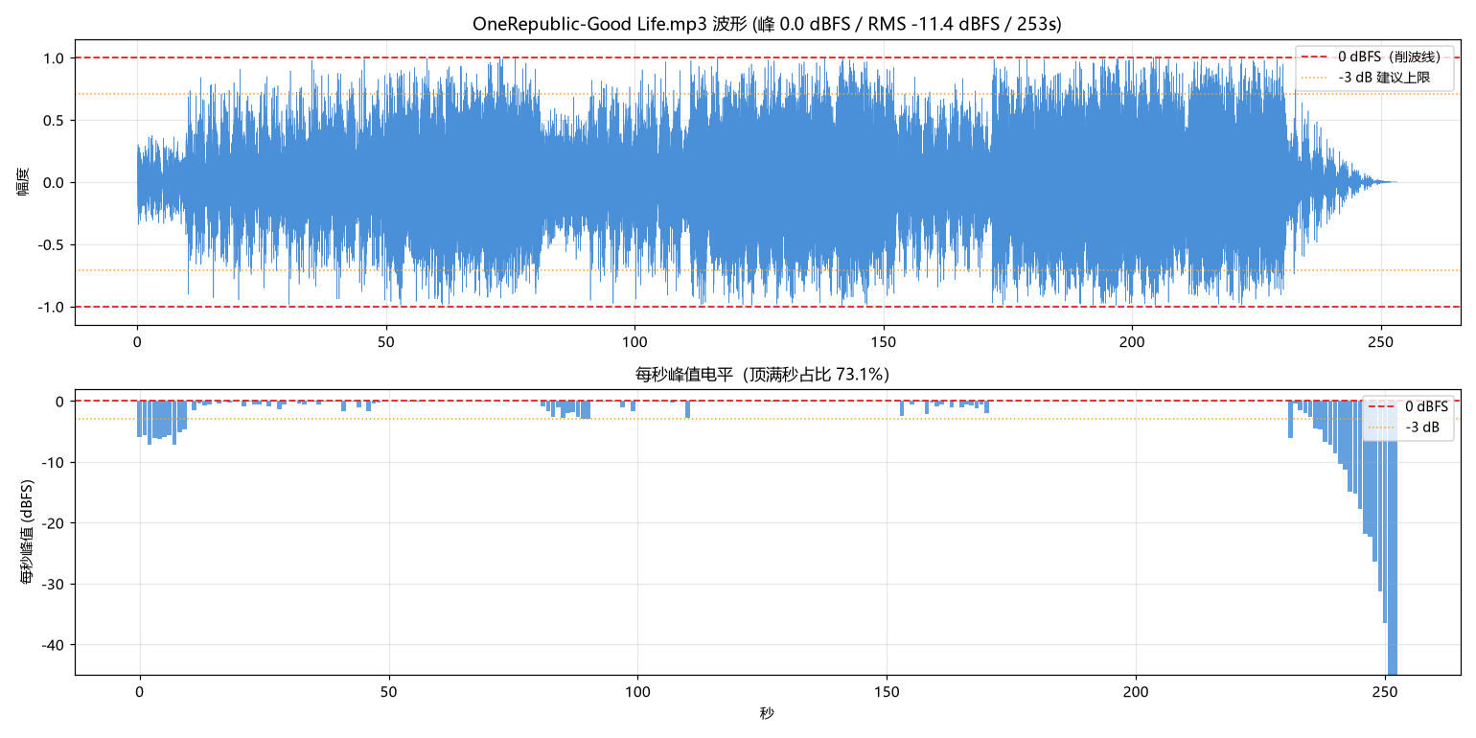
docs/audio-guard/OneRepublic-Good-Life-波形分析.png
