cfy2012/memoria-os/docs/audio-guard/PERFECT-GIRL-FUNK-波形分析.png

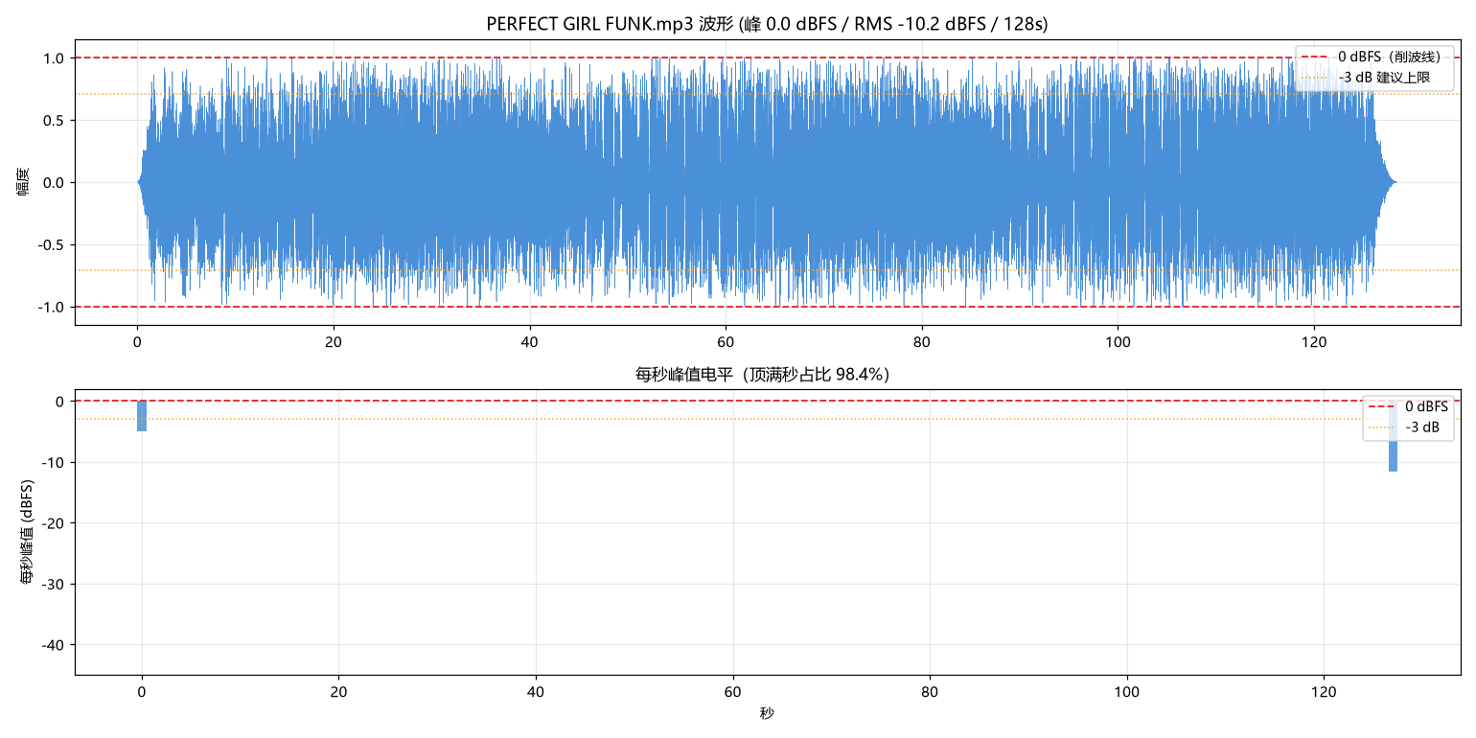
docs/audio-guard/PERFECT-GIRL-FUNK-波形分析.png
