cfy2012/memoria-os/docs/audio-guard/REVENGE-波形分析.png

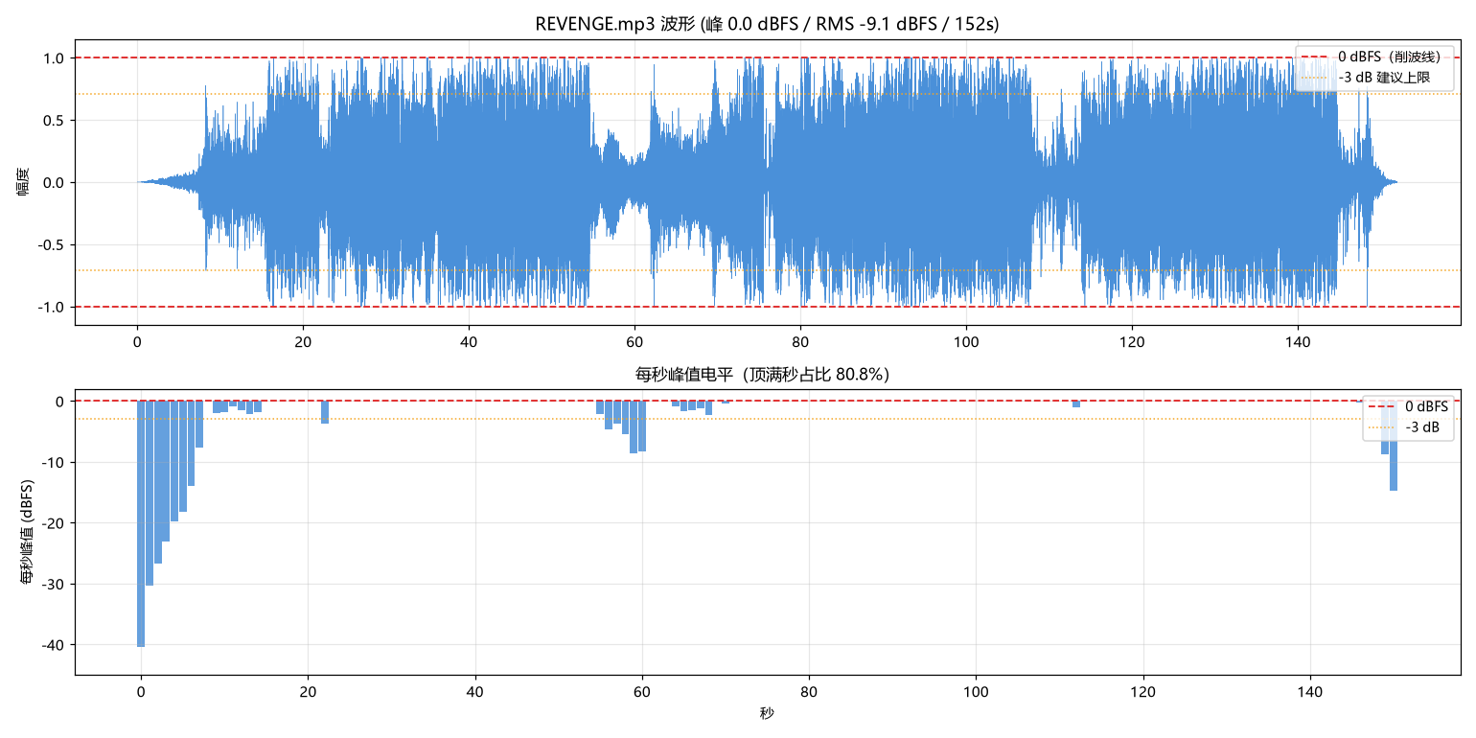
docs/audio-guard/REVENGE-波形分析.png
