cfy2012/memoria-os/docs/audio-guard/SPOOKY-波形分析.png

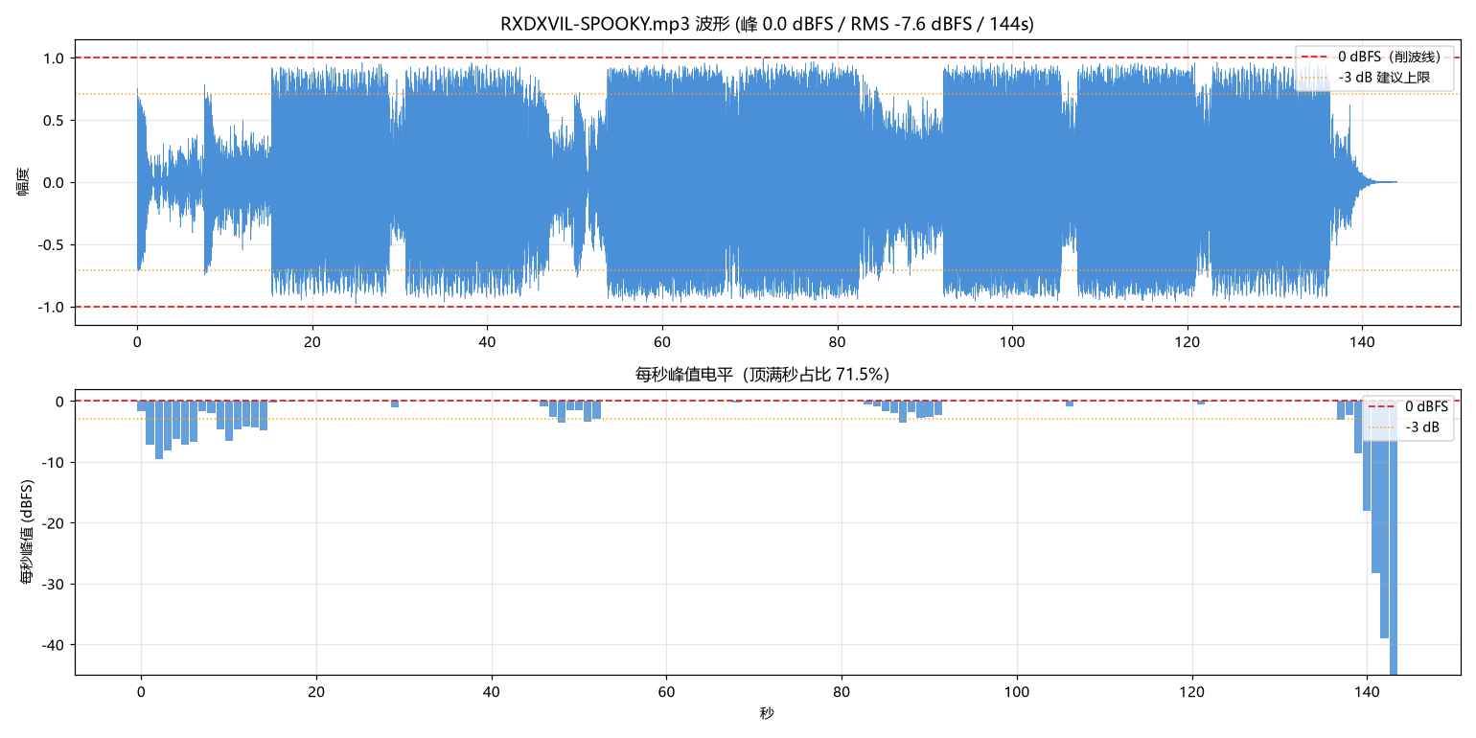
docs/audio-guard/SPOOKY-波形分析.png
