cfy2012/memoria-os/docs/audio-guard/TAKEDISKRUSH-波形分析.png

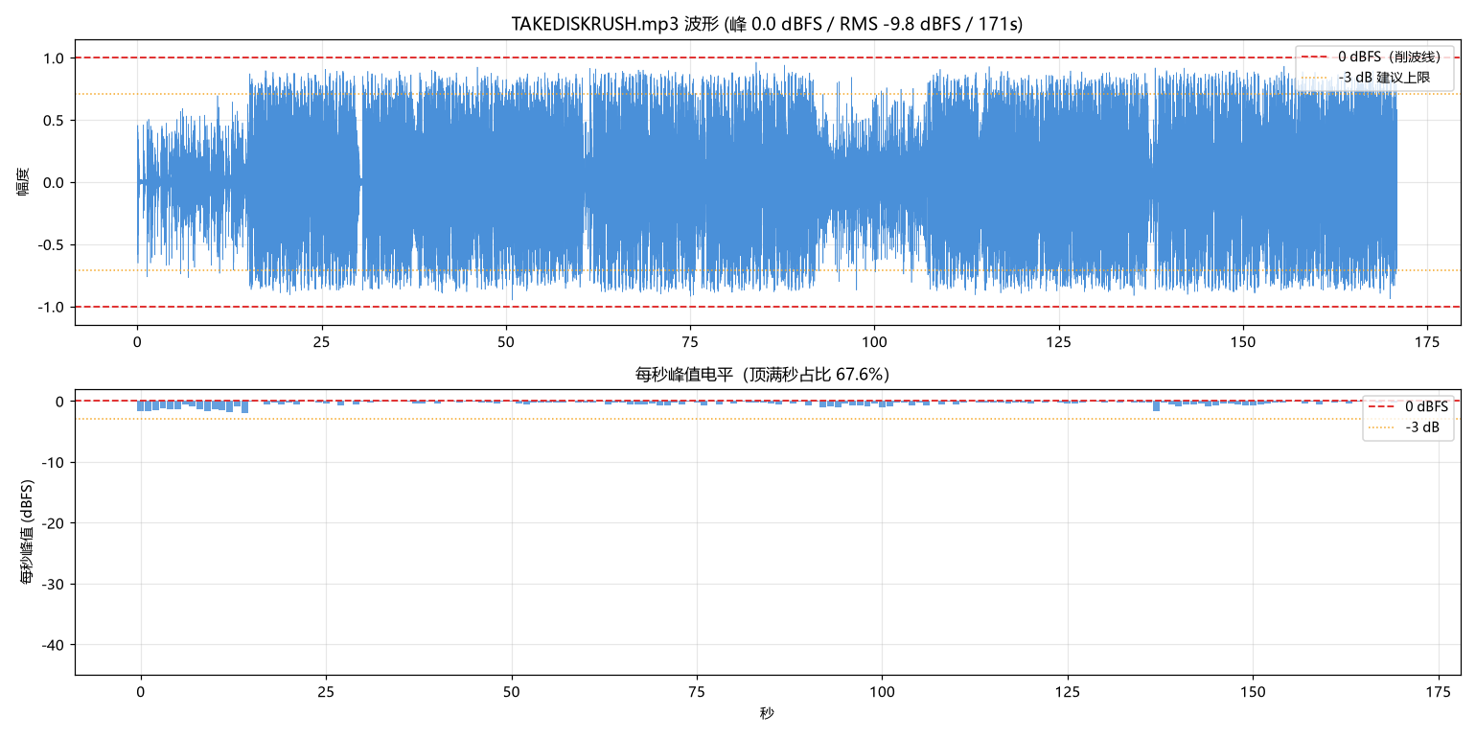
docs/audio-guard/TAKEDISKRUSH-波形分析.png
