cfy2012/memoria-os/docs/audio-guard/THE-INVINCIBLE-KING-2-波形分析.png

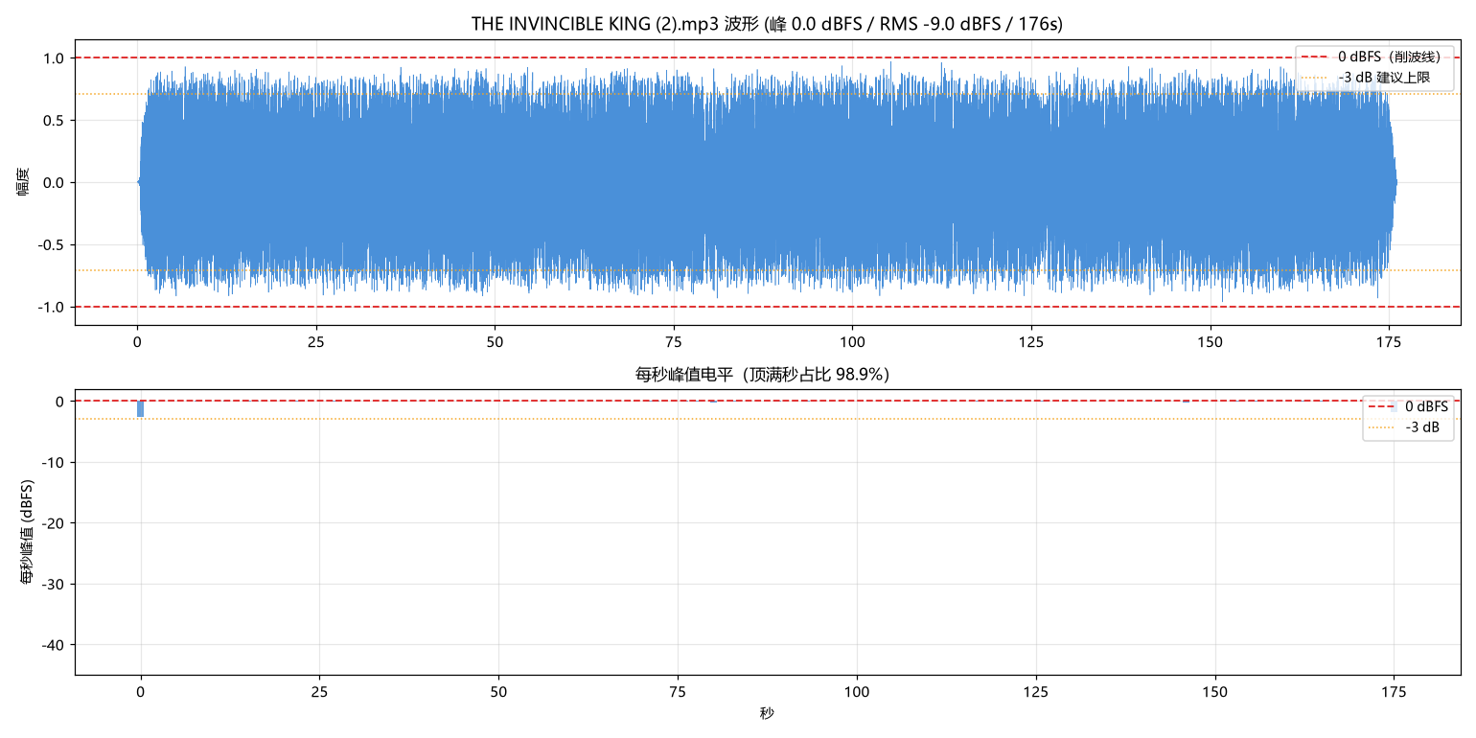
docs/audio-guard/THE-INVINCIBLE-KING-2-波形分析.png
