cfy2012/memoria-os/docs/audio-guard/The-Invincible-King-波形分析.png

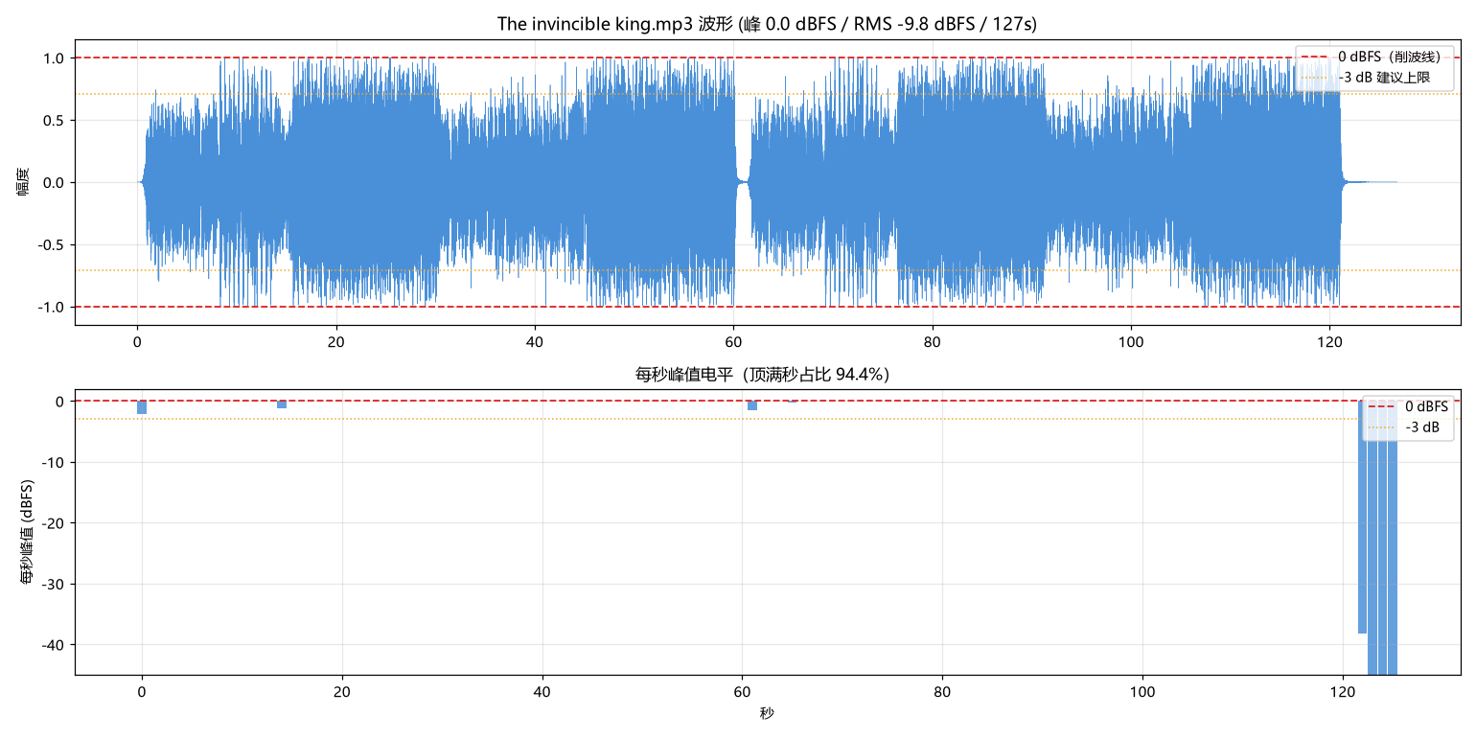
docs/audio-guard/The-Invincible-King-波形分析.png
