cfy2012/memoria-os/docs/audio-guard/TIKI-TIKI-波形分析.png

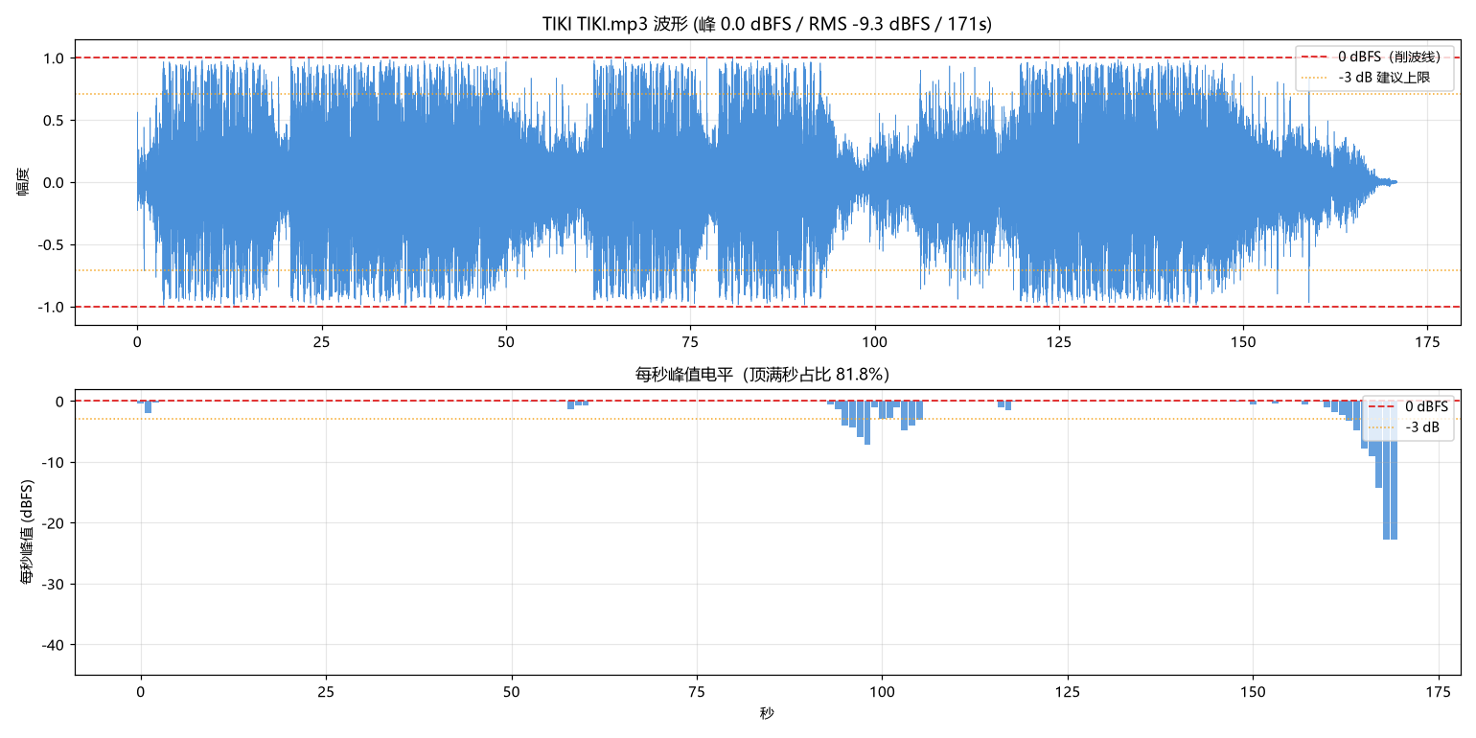
docs/audio-guard/TIKI-TIKI-波形分析.png
