cfy2012/memoria-os/docs/audio-guard/UNA-MAS-FUNK-2-波形分析.png

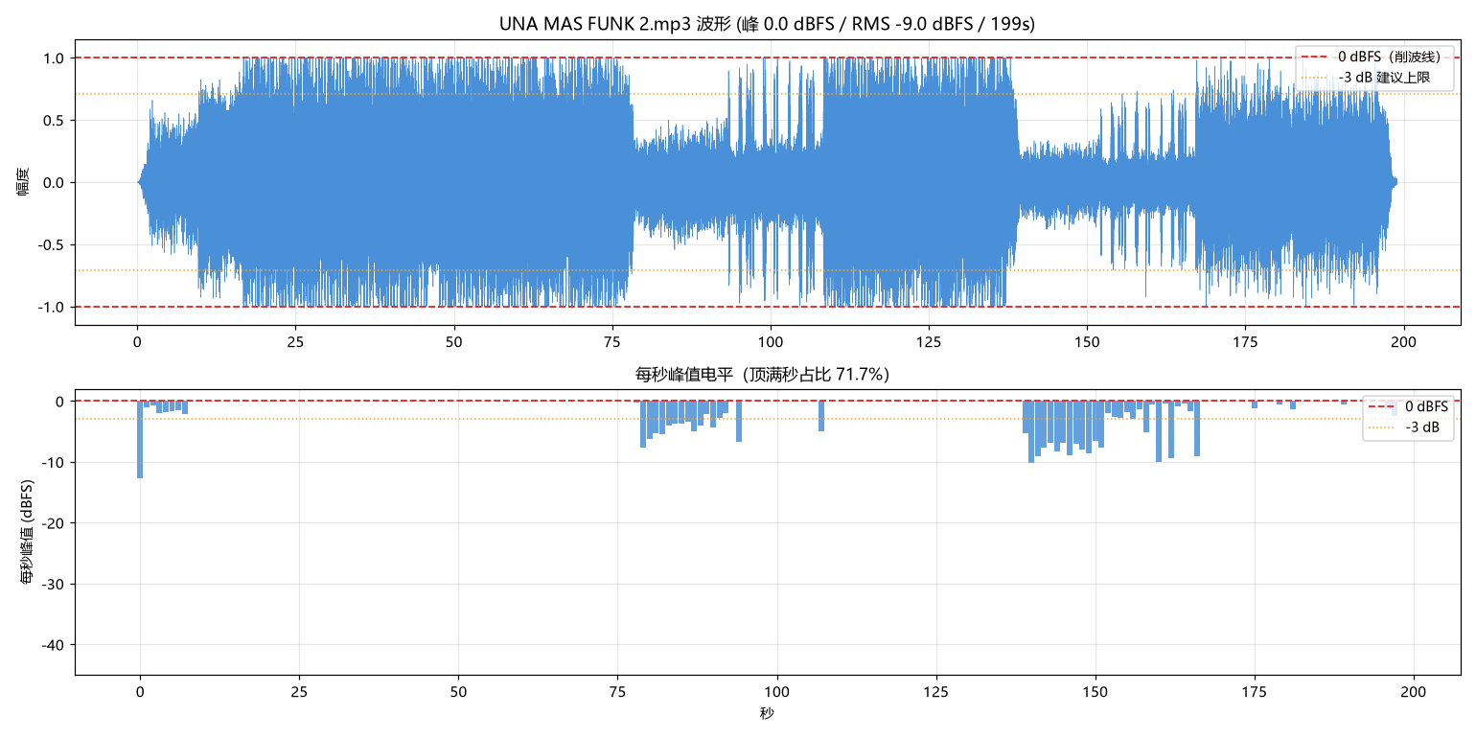
docs/audio-guard/UNA-MAS-FUNK-2-波形分析.png
