cfy2012/memoria-os/docs/audio-guard/UNA-MAS-波形分析.png

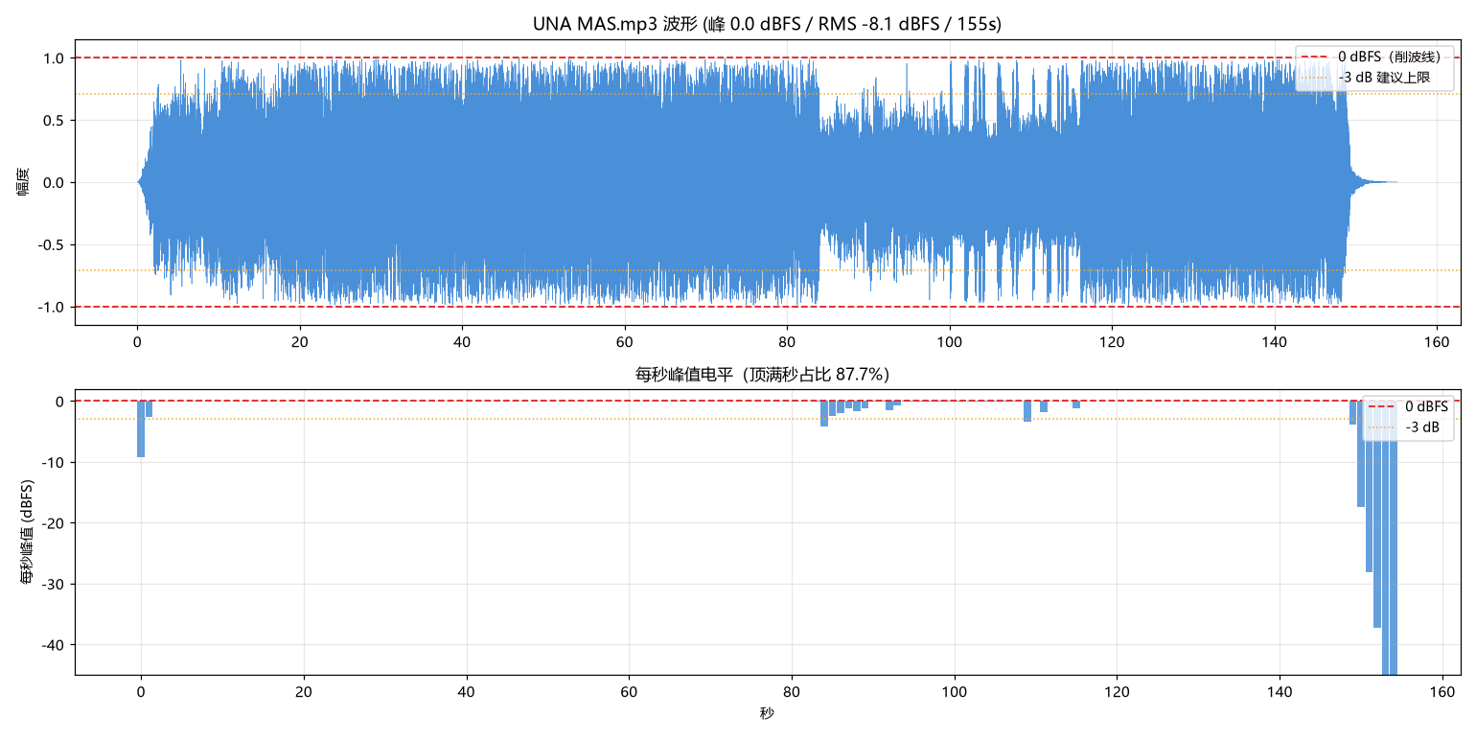
docs/audio-guard/UNA-MAS-波形分析.png
