cfy2012/memoria-os/docs/audio-guard/UNICUBE-波形分析.png

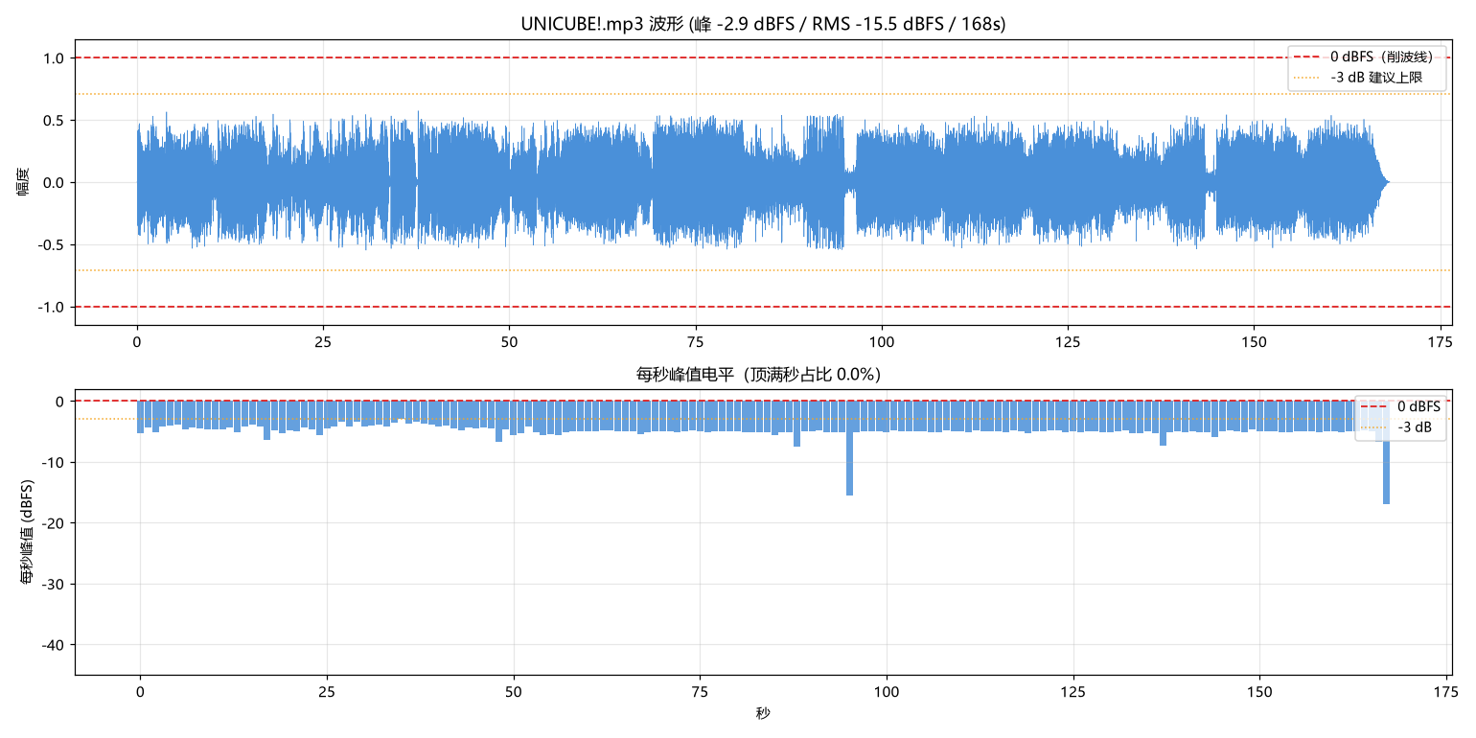
docs/audio-guard/UNICUBE-波形分析.png
