cfy2012/memoria-os/docs/audio-guard/WINTER-FEELS-LIKE-FUNK-波形分析.png

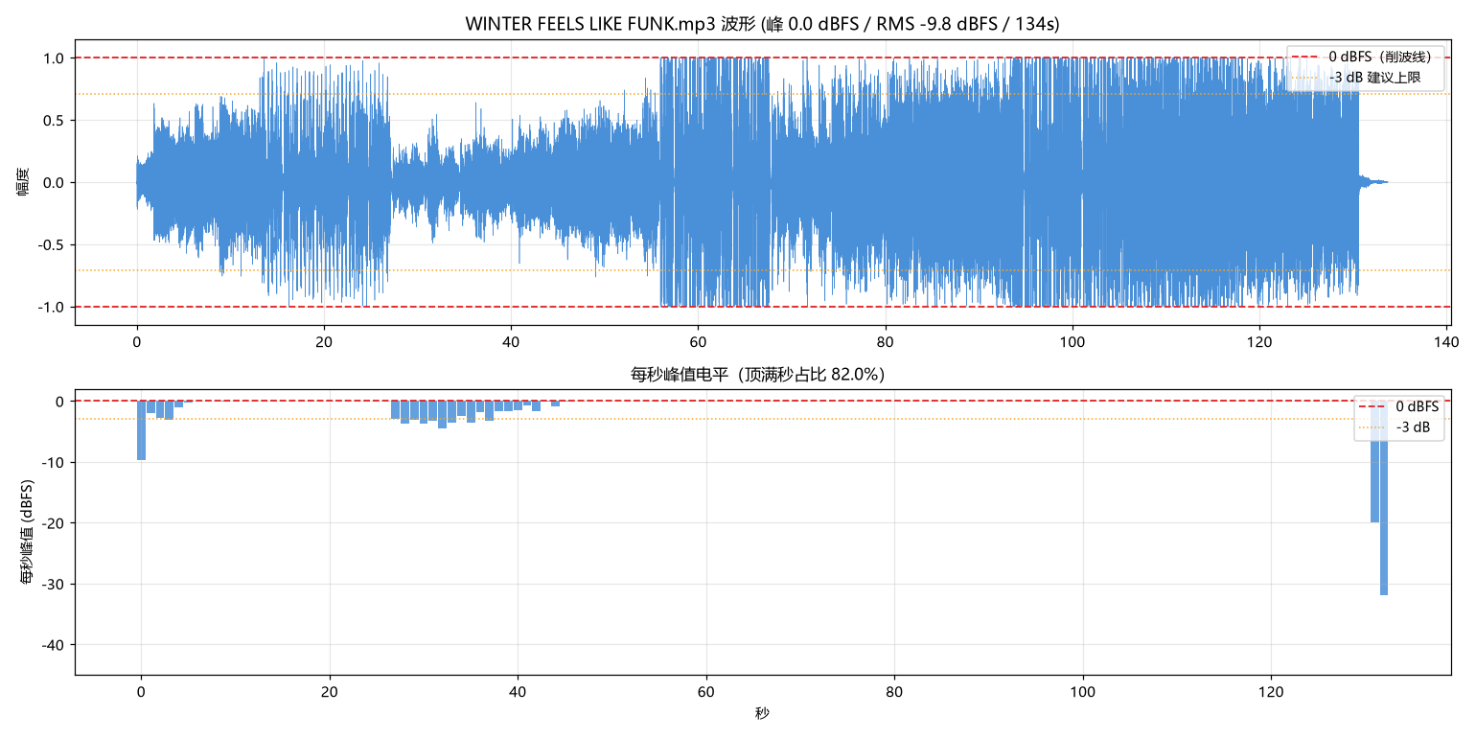
docs/audio-guard/WINTER-FEELS-LIKE-FUNK-波形分析.png
