cfy2012/memoria-os/docs/audio-guard/X-COOL-波形分析.png

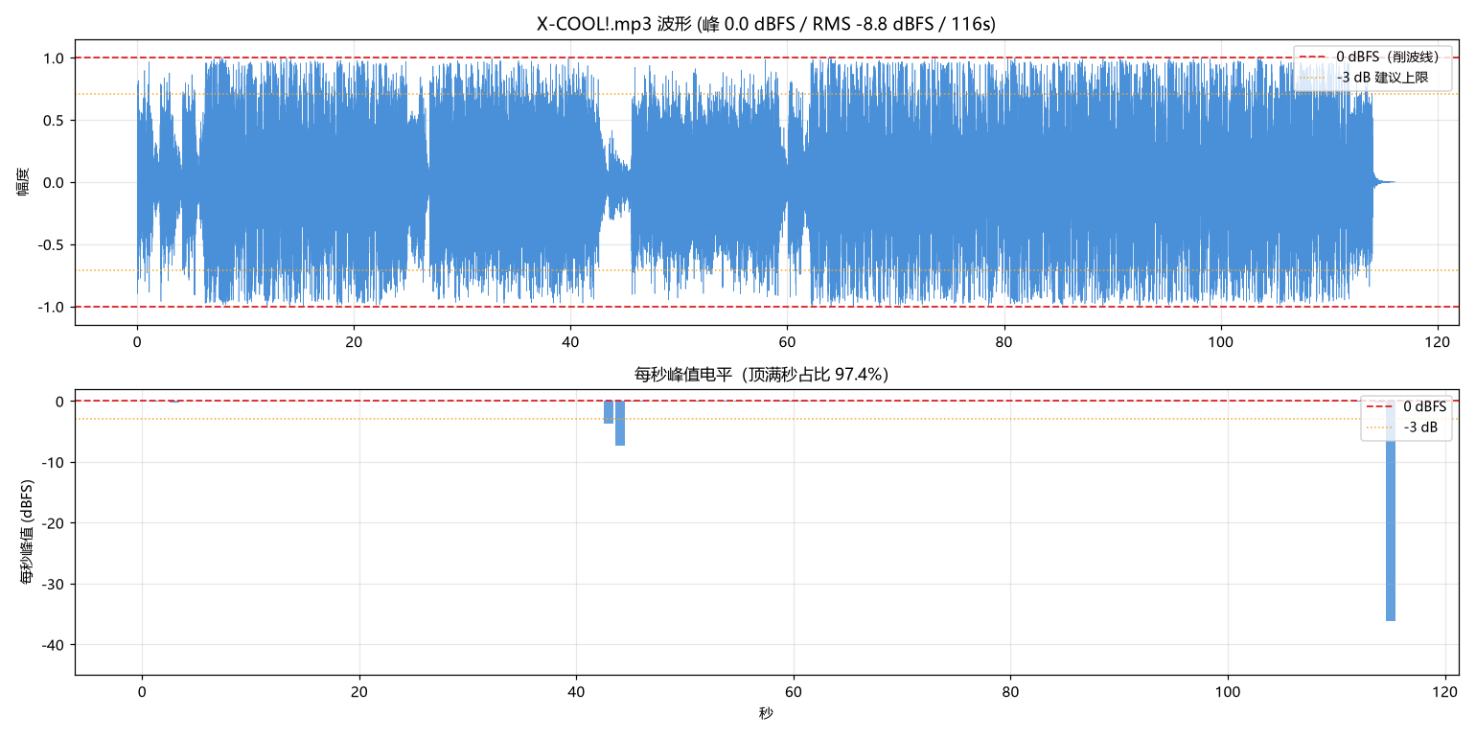
docs/audio-guard/X-COOL-波形分析.png
