cfy2012/memoria-os/docs/audio-guard/加勒比海盗-波形分析.png

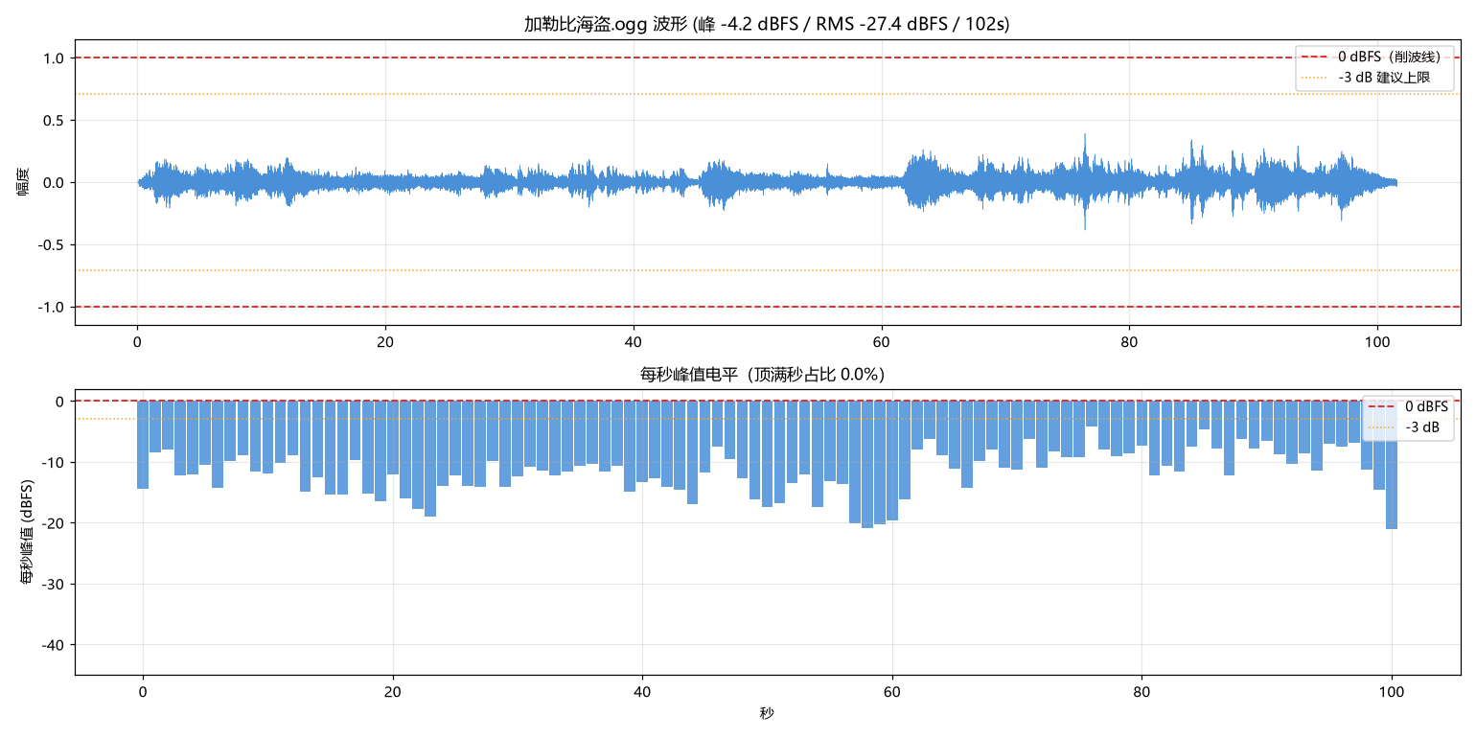
docs/audio-guard/加勒比海盗-波形分析.png
