cfy2012/memoria-os/docs/audio-guard/反乌托邦-波形分析.png

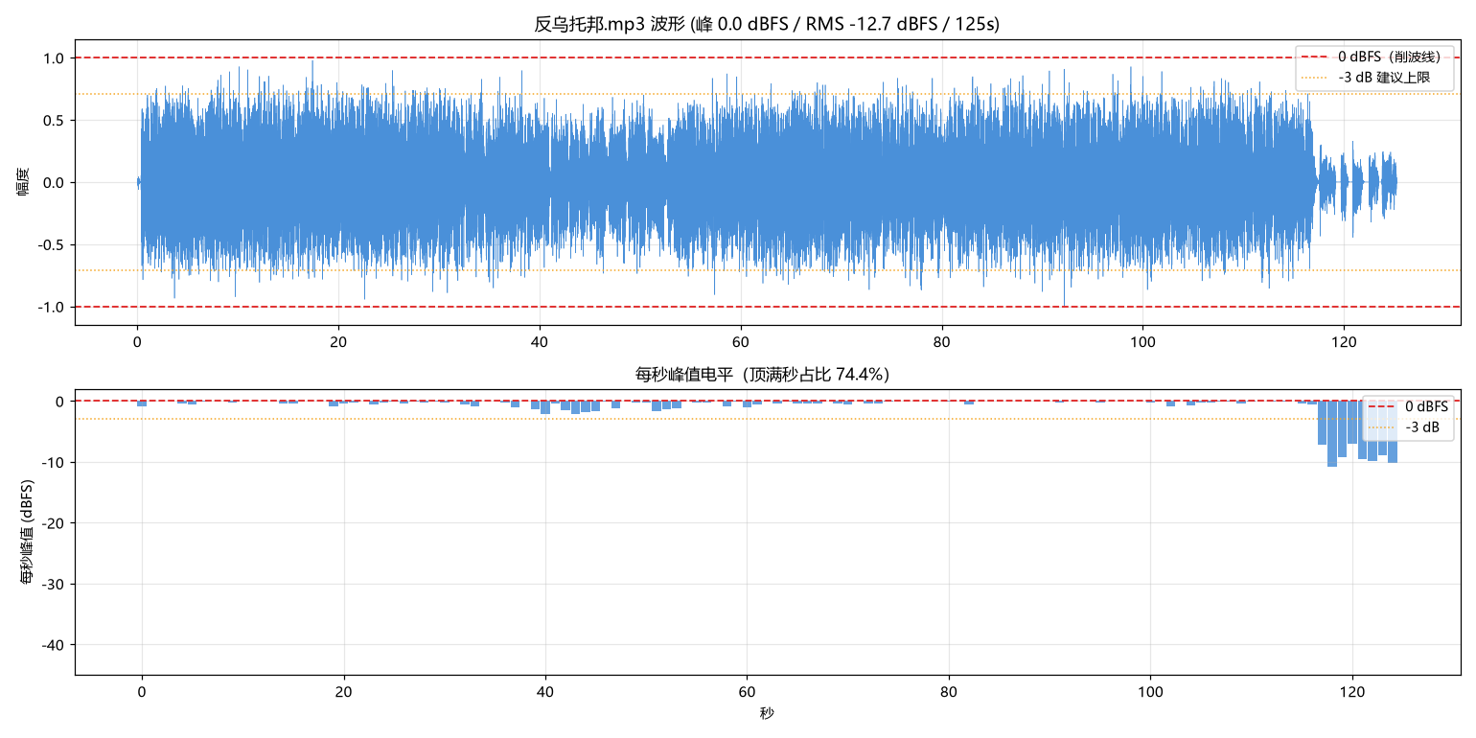
docs/audio-guard/反乌托邦-波形分析.png
