cfy2012/memoria-os/docs/audio-guard/嘉晚宁-归零魔鬼花园-波形分析.png

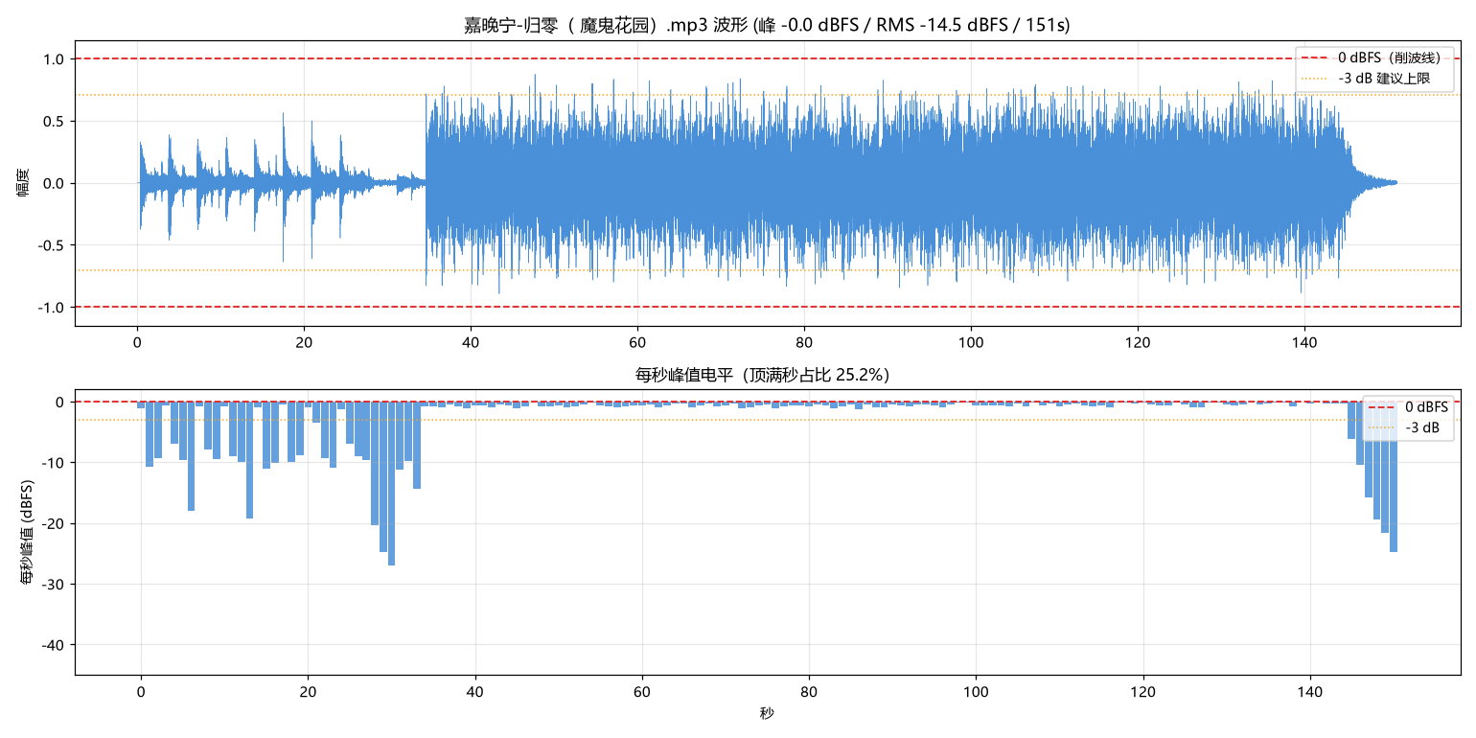
docs/audio-guard/嘉晚宁-归零魔鬼花园-波形分析.png
