cfy2012/memoria-os/docs/audio-guard/夜，萤火虫和你-波形分析.png

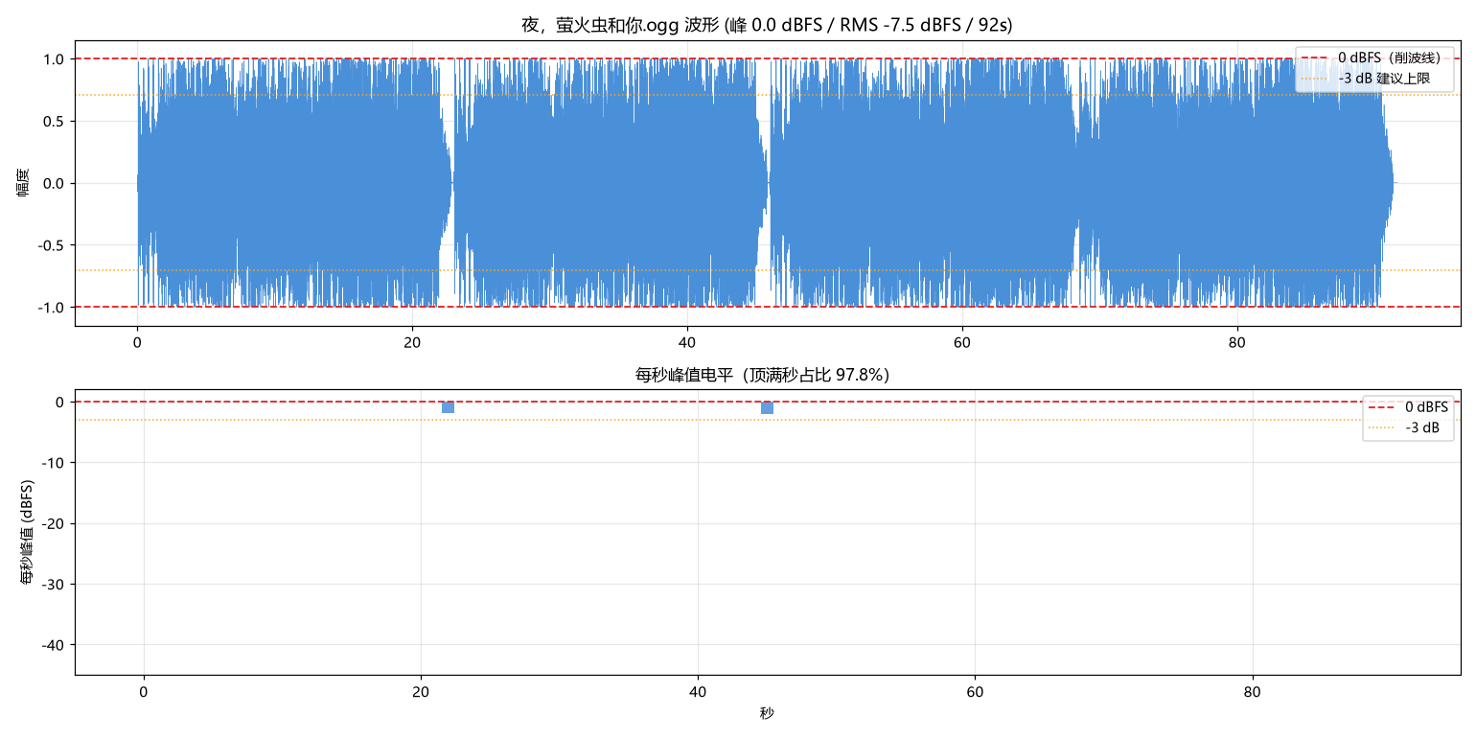
docs/audio-guard/夜，萤火虫和你-波形分析.png
