cfy2012/memoria-os/docs/audio-guard/查理九世-波形分析.png

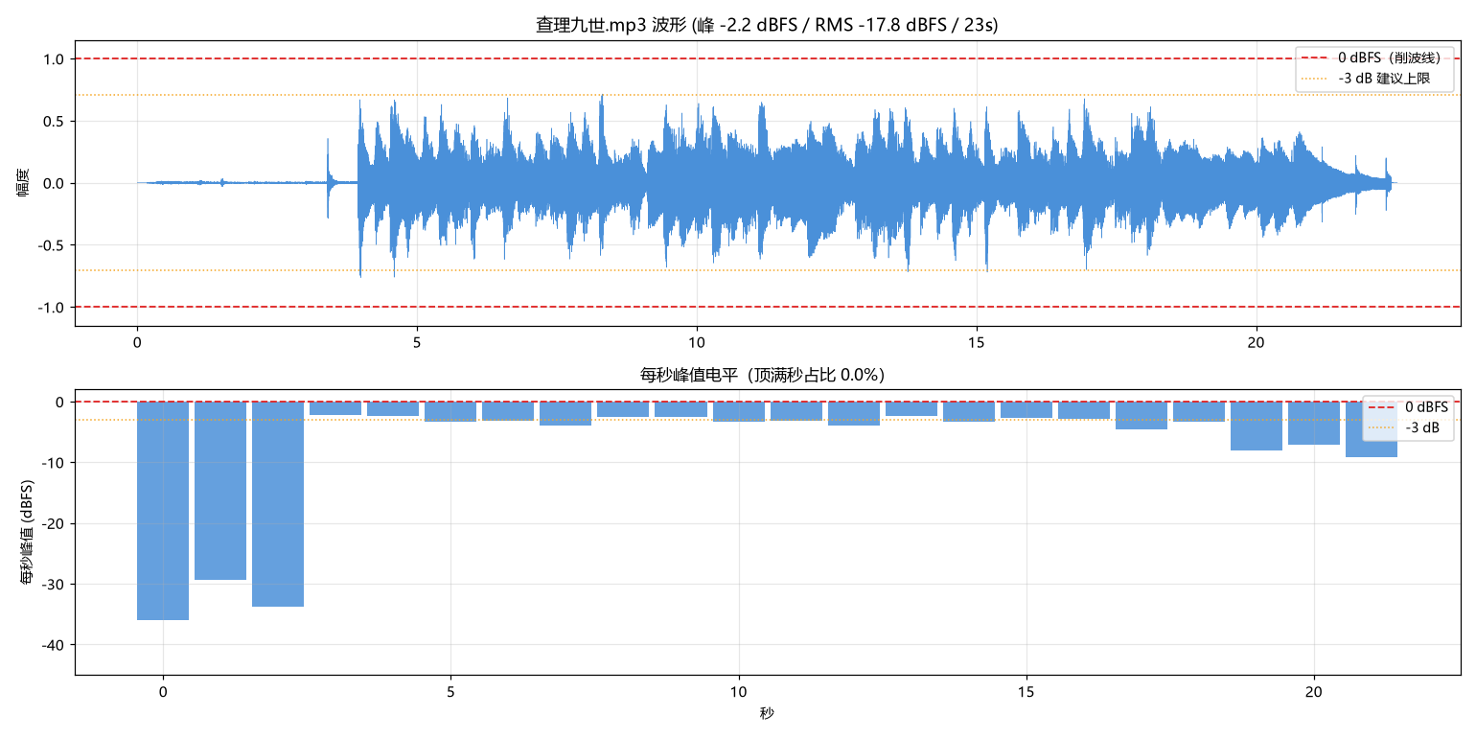
docs/audio-guard/查理九世-波形分析.png
