cfy2012/memoria-os/docs/audio-guard/王浩-异客-cover：-杨坤丨王赫野丨王睿卓-Live-波形分析.png

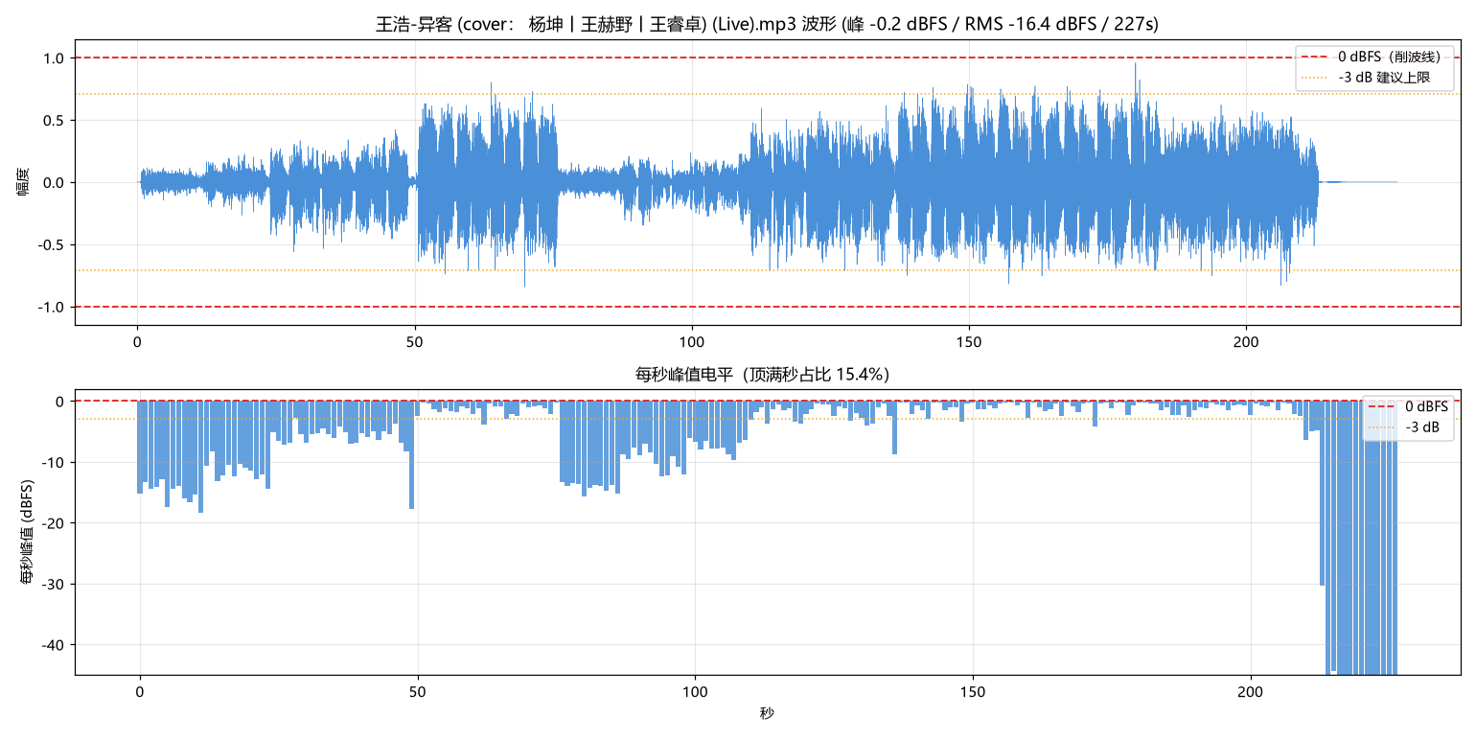
docs/audio-guard/王浩-异客-cover：-杨坤丨王赫野丨王睿卓-Live-波形分析.png
