cfy2012/memoria-os/docs/audio-guard/糯米Nomi-调查中-变速版-波形分析.png

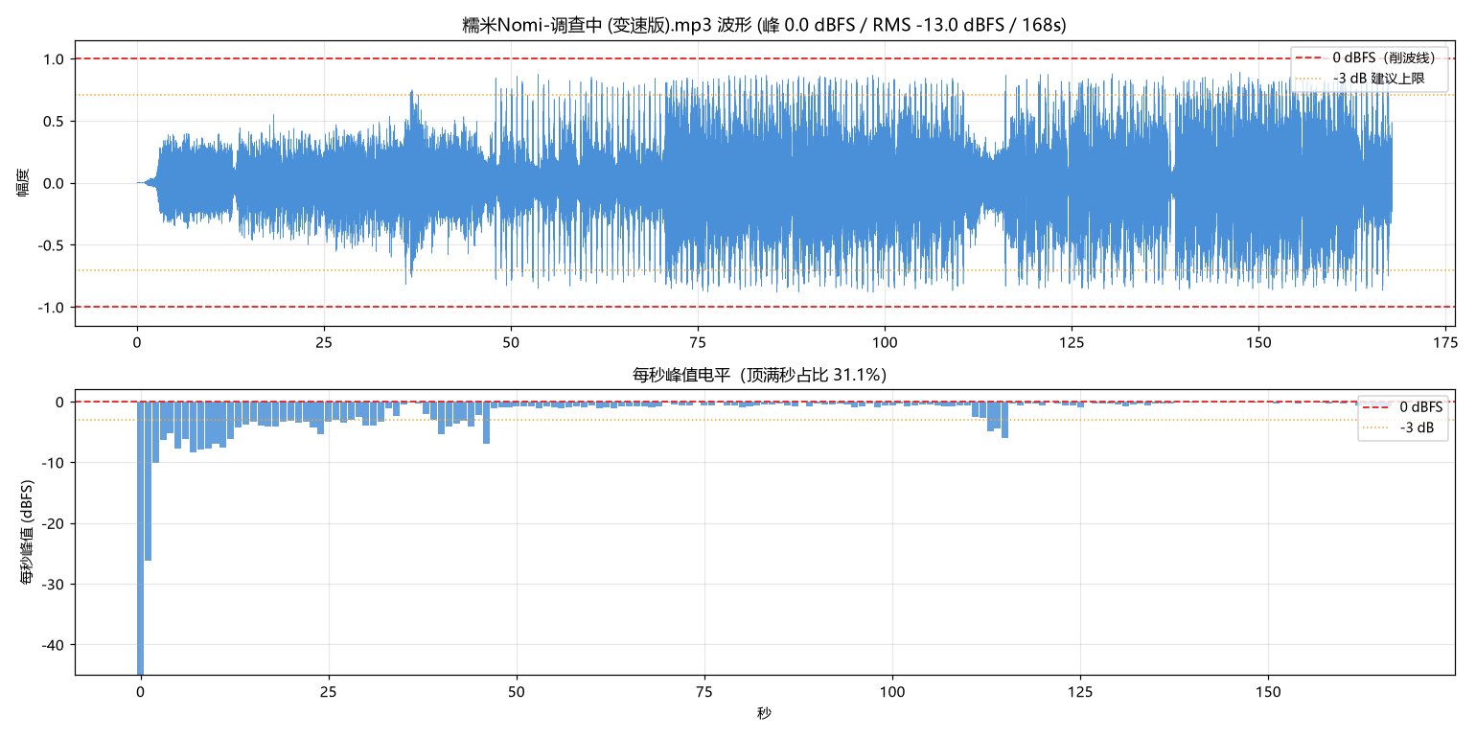
docs/audio-guard/糯米Nomi-调查中-变速版-波形分析.png
