cfy2012/memoria-os/docs/audio-guard/郭顶-凄美地-波形分析.png

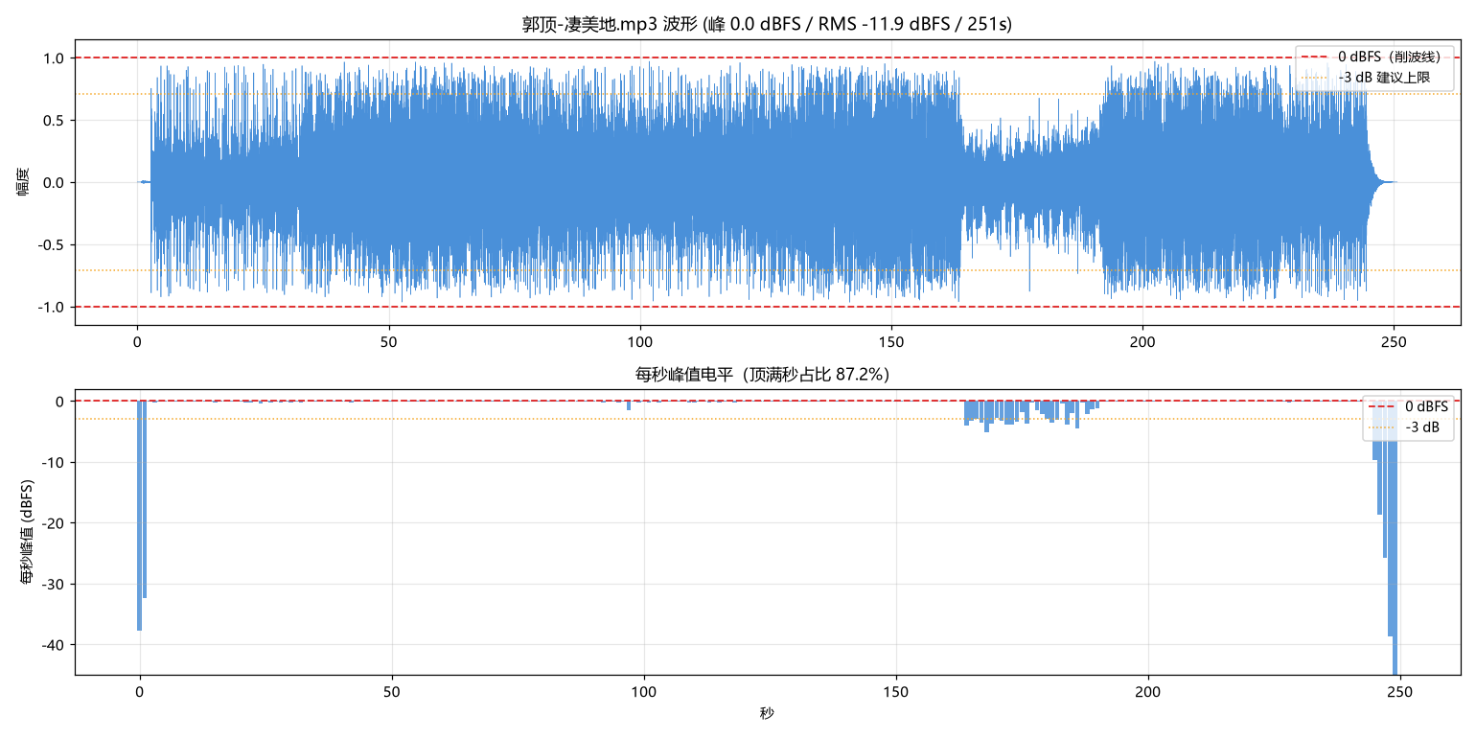
docs/audio-guard/郭顶-凄美地-波形分析.png
