cfy2012/memoria-os/docs/audio-guard/MONTAGEM-ALQUIMIA-波形分析.png

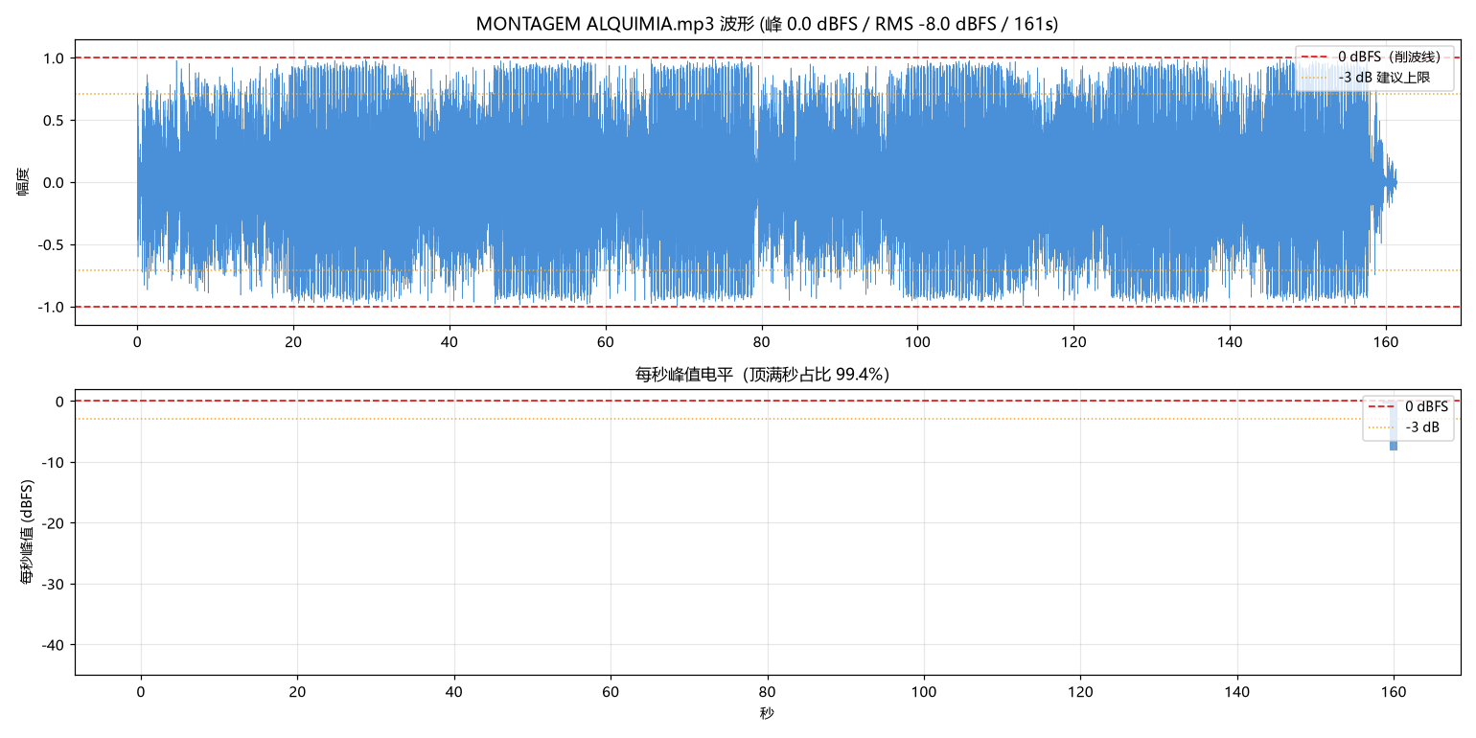
docs/audio-guard/MONTAGEM-ALQUIMIA-波形分析.png
