cfy2012/memoria-os/docs/audio-guard/MONTAGEM-CORAL-波形分析.png

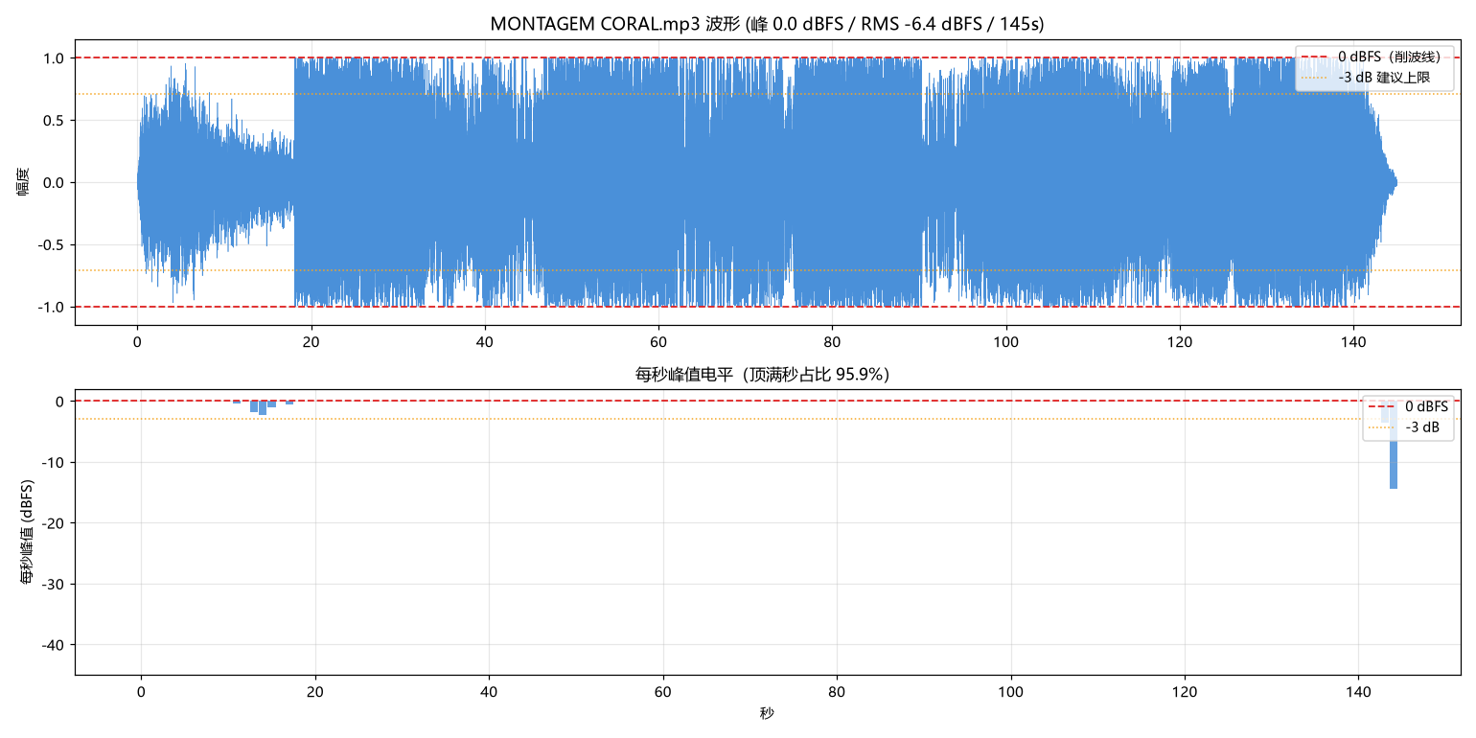
docs/audio-guard/MONTAGEM-CORAL-波形分析.png
