cfy2012/memoria-os/docs/audio-guard/Montagem-Nada-Tropica-2-波形分析.png

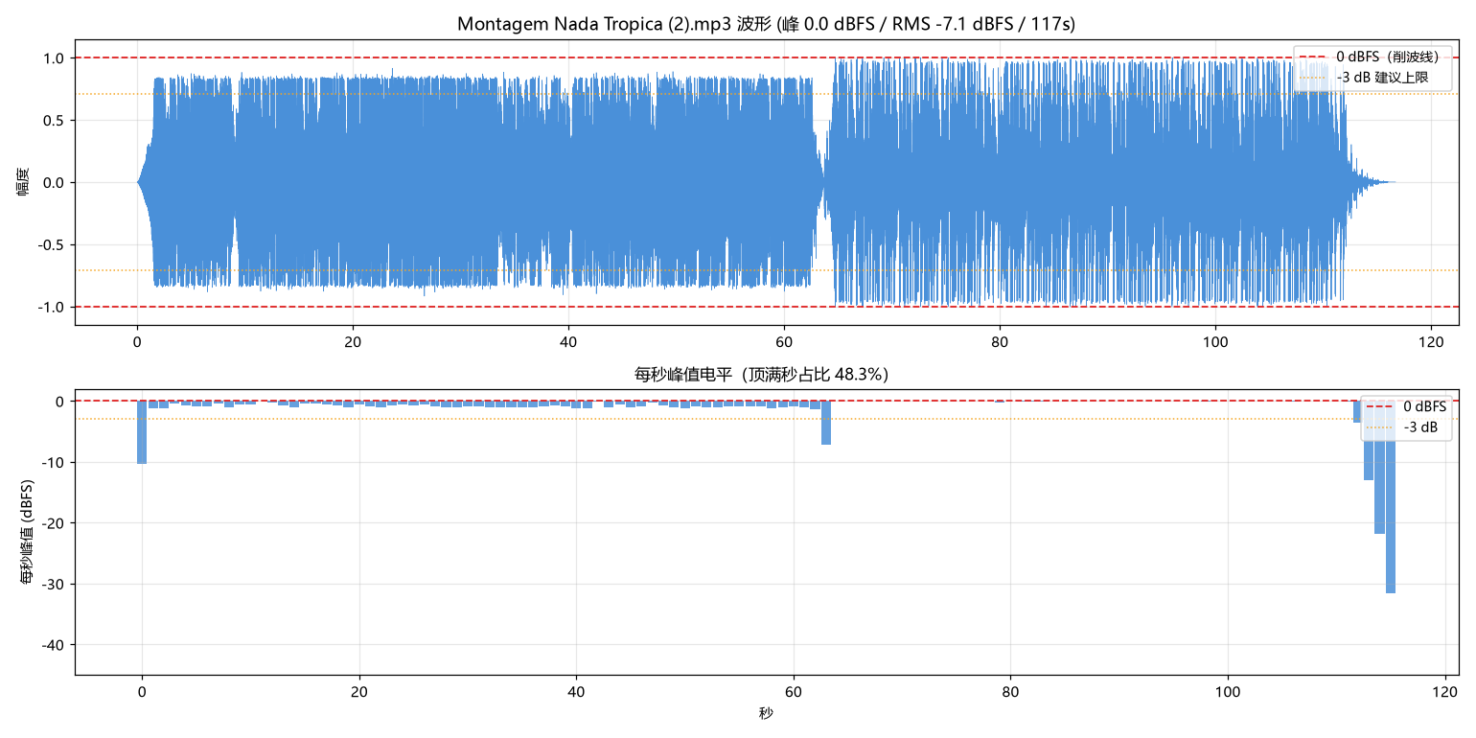
docs/audio-guard/Montagem-Nada-Tropica-2-波形分析.png
