cfy2012/memoria-os/docs/验收-SETUP网络管理-WiFi.png

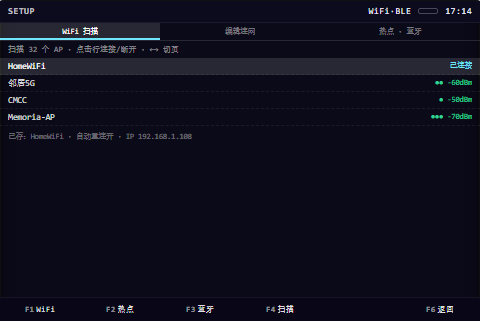
docs/验收-SETUP网络管理-WiFi.png
