cfy2012/memoria-os/docs/验收-SETUP网络管理-热点蓝牙.png

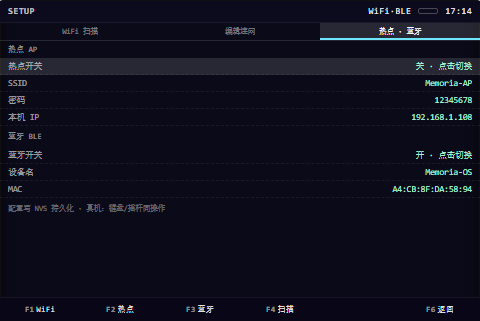
docs/验收-SETUP网络管理-热点蓝牙.png
